JonTeaCz/CECS490-DR.PILL/Progress/Presentations/CECS 490A Progress Presentation 2.pdf

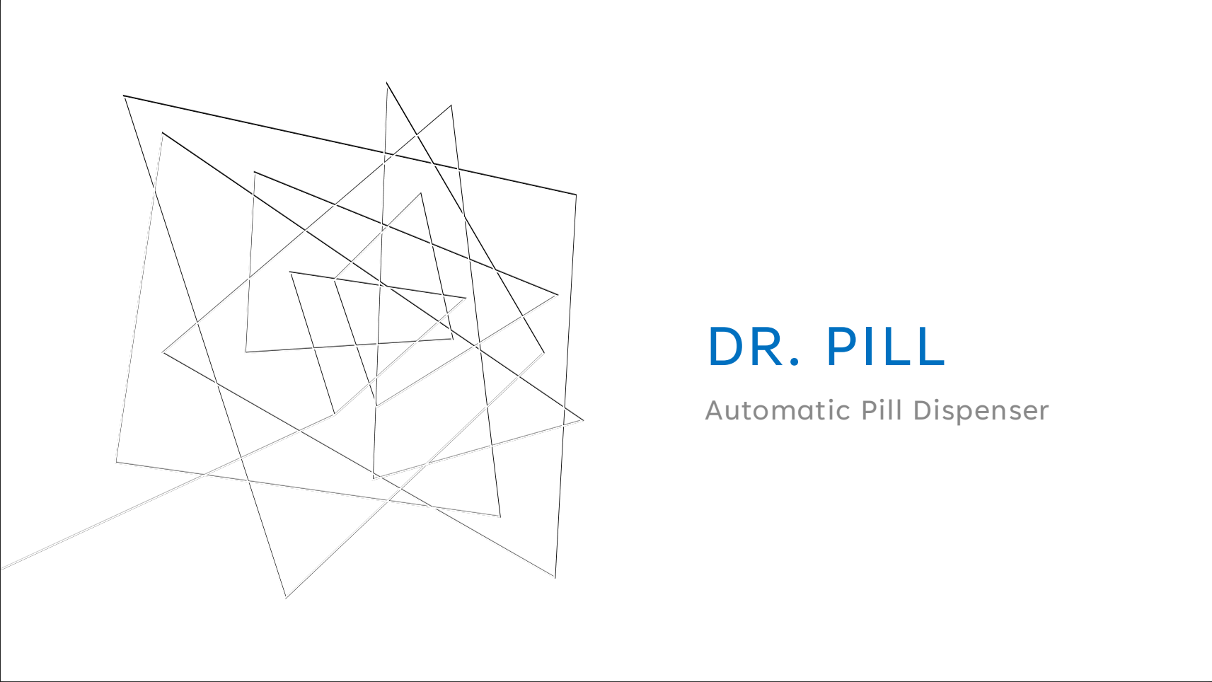
[picture p87: page 1]

# DR. PILL

# Automatic Pill Dispenser

# TEAM & ROLES

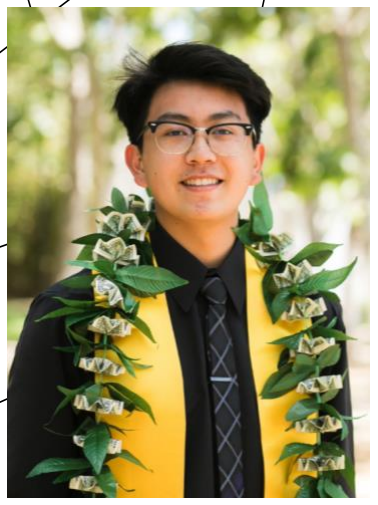
[picture p88: figure]

### - Power Supply & Regulation

## Jonathan Cerniaz

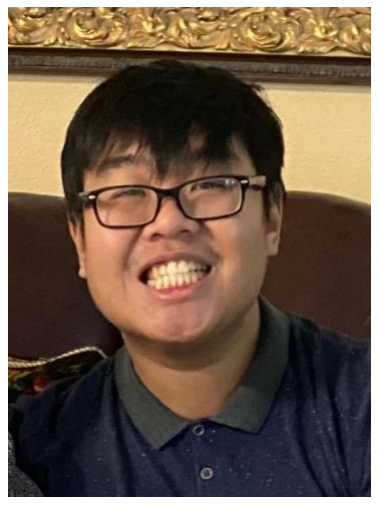
[picture p89: figure]

## Jehmel Espiritu

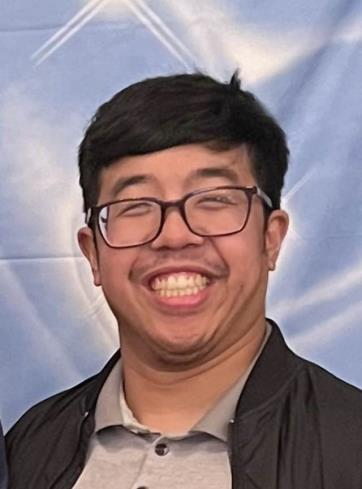
[picture p90: figure]

## Jeremy Espiritu

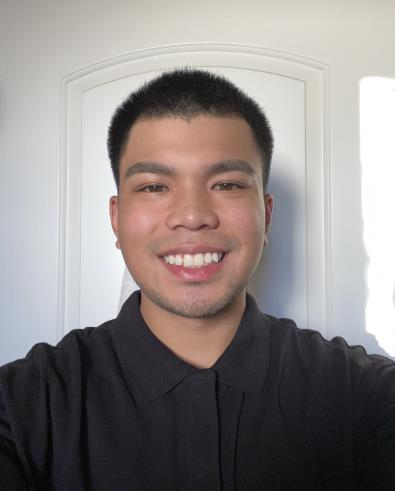
[picture p91: figure]

## Joseph Guzman

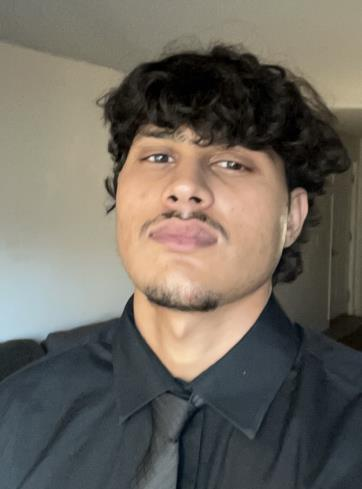
[picture p92: figure]

## Afzal Hakim

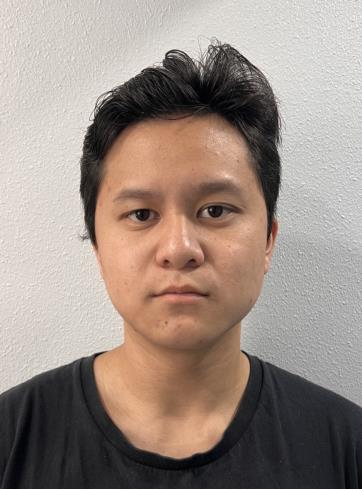
[picture p93: figure]

## Lee Roger Ordinario

### - Software Development of Interface

### - Log tracking and Security

### - Pill Storage System and Organization

### - Software Development of Interface

### - 3D Designing and Motor Testing for dispense mechanism

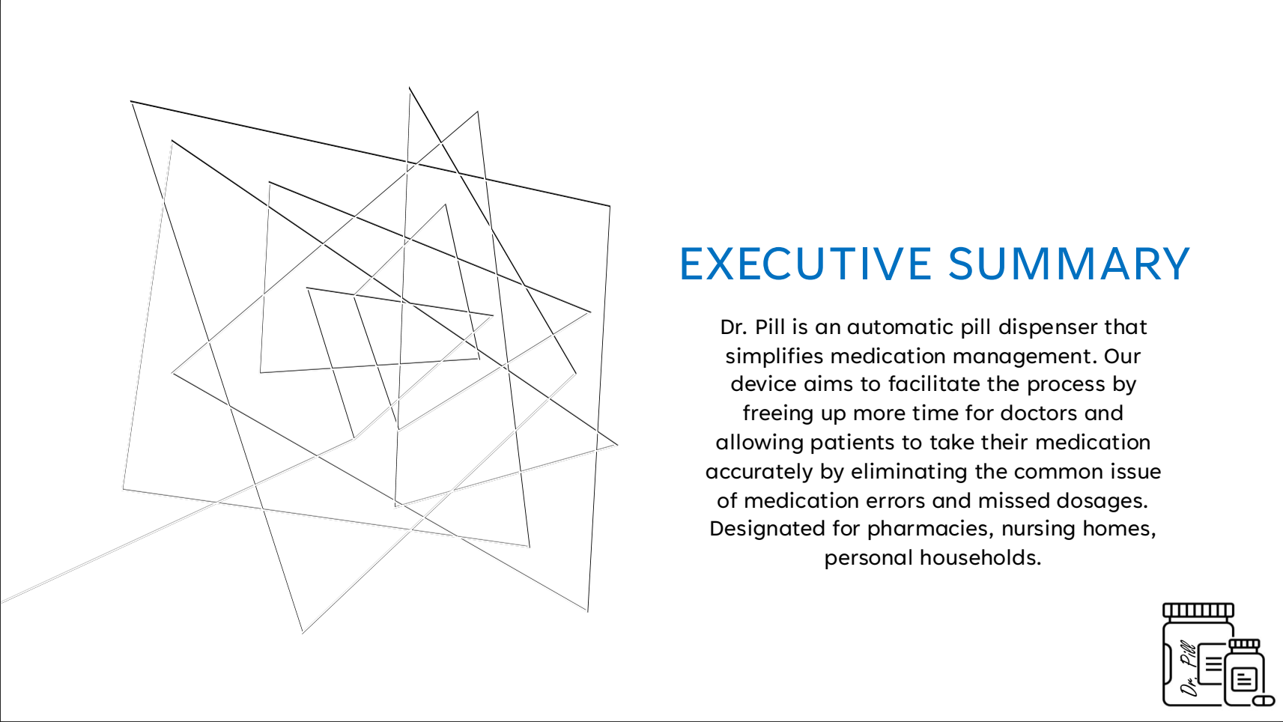
[picture p94: page 3]

# EXECUTIVE SUMMARY

## Dr. Pill is an automatic pill dispenser that simplifies medication management. Our device aims to facilitate the process by freeing up more time for doctors and allowing patients to take their medication accurately by eliminating the common issue

of medication errors and missed dosages. Designated for pharmacies, nursing homes, personal households.

## Dr. Pill

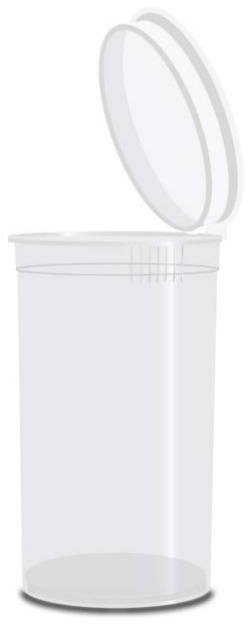
[picture p95: figure]
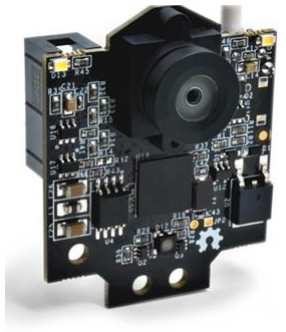
[picture p96: figure]

DISPENSE MECHANISM • Two Modes: Refill and On-demand o Refill: continuous dispensing of multiple pills

## of the same type

- On

## -demand: Needed number of dosage

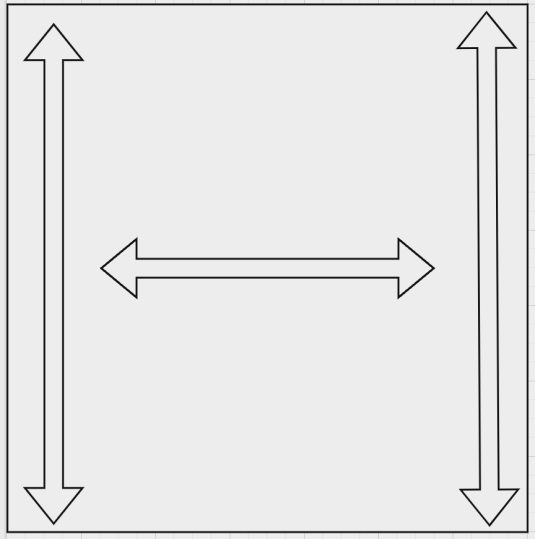
[picture p97: figure]

## dispensed at scheduled time

## - Object Recognition o To verify pill characteristics (color, size, pill

## shape, markings)

- Loading Mechanism for Grid o Use of Clear Prescription Bottles for visibility o Cross-contamination Prevention

## Dr. Pill Dr. Pill

## Features

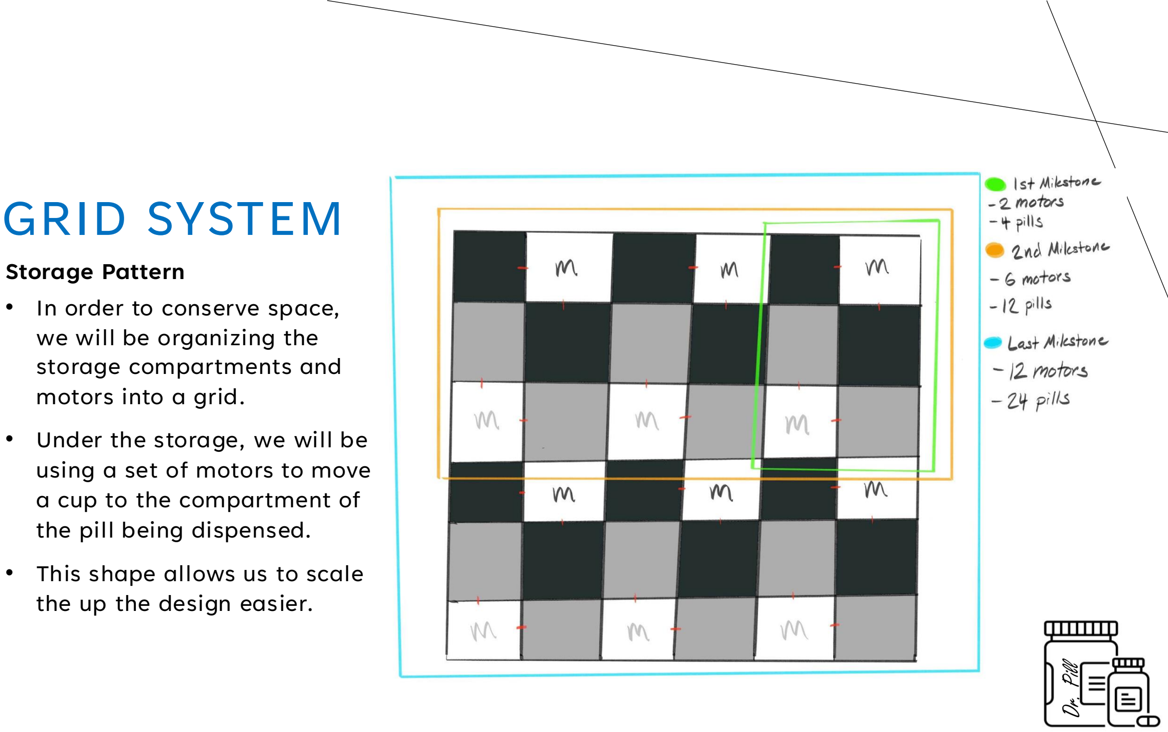
[picture p98: page 5]

# GRID SYSTEM

## Dr. Pill

## Storage Pattern

## Dr. Pill

- In order to conserve space,

## we will be organizing the storage compartments and

motors into a grid.

## - Under the storage, we will be using a set of motors to move a cup to the compartment of

the pill being dispensed.

## - This shape allows us to scale

the up the design easier.

# XAMPP

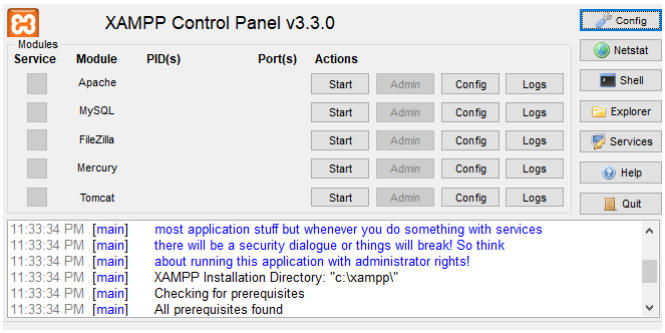
[picture p99: figure]

## Dr. Pill Dr. Pill

## - MySQL Database: We use this to store and manage logs such as user login

activity and pill requests.

## - Apache Server : This serves as the web server to handle user requests and

process PHP scripts.

# MYSQL DATABASE

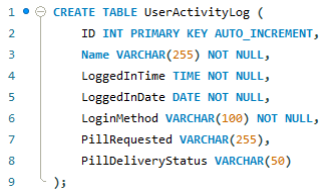
[picture p100: figure]

## Example code showing how the table columns for storing the data will be

structured.

## Dr. Pill Dr. Pill

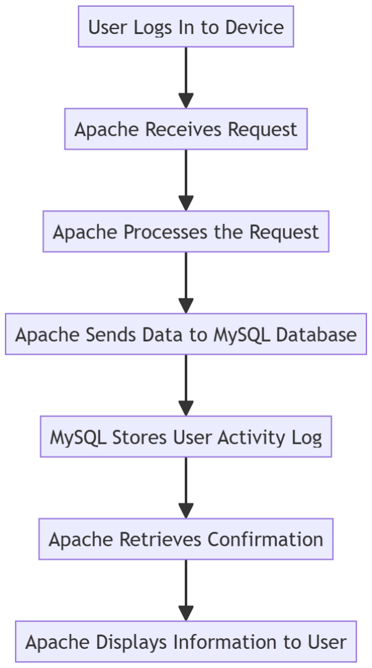
[picture p101: figure]

# APACHE

## Dr. Pill Dr. Pill

## - When a request is made for a PHP file, Apache processes the PHP code through the PHP interpreter in XAMPP and sends

the output back to the device.

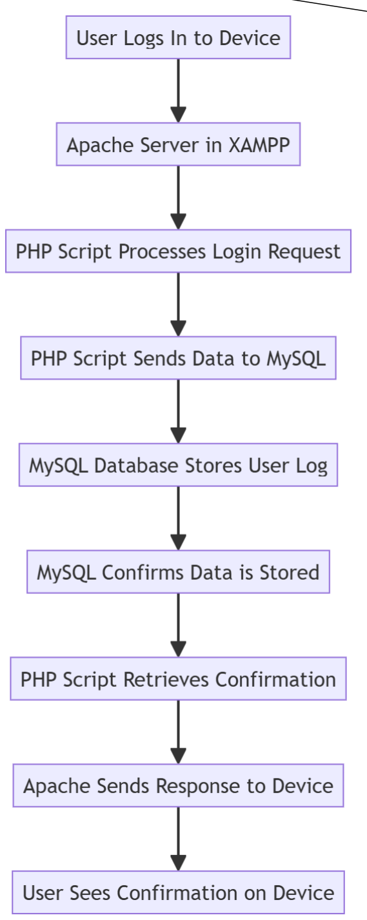
[picture p102: figure]

9

# SIMPLE FLOWCHART OF LOG TRACKING

# INTERFACE

## Features

## - User Authentication: uses MySQL database for secure login and credential storage

## - MySQL Database Integration: Central for storing user data, patient records, staff actions and logs

## - Permission checks: ensure secure, authorized actions

## - Guidance Prompts: if patient is denied, directs them to seek assistance with logs recorded

## Dr. Pill Dr. Pill

## Staff/Patient Input

## - Staff Input

## - Storage Management: Check and update inventory

## - Patient Management: Add/remove patient records

## - Logs Management: View history data

- Medication Retrieval: staff can retrieve medication,

## with actions logged onto the database

## - Patient Input

- Medication Retrieval: Permission-based access,

## logged onto the database

## - View History log: Patients access personal logs

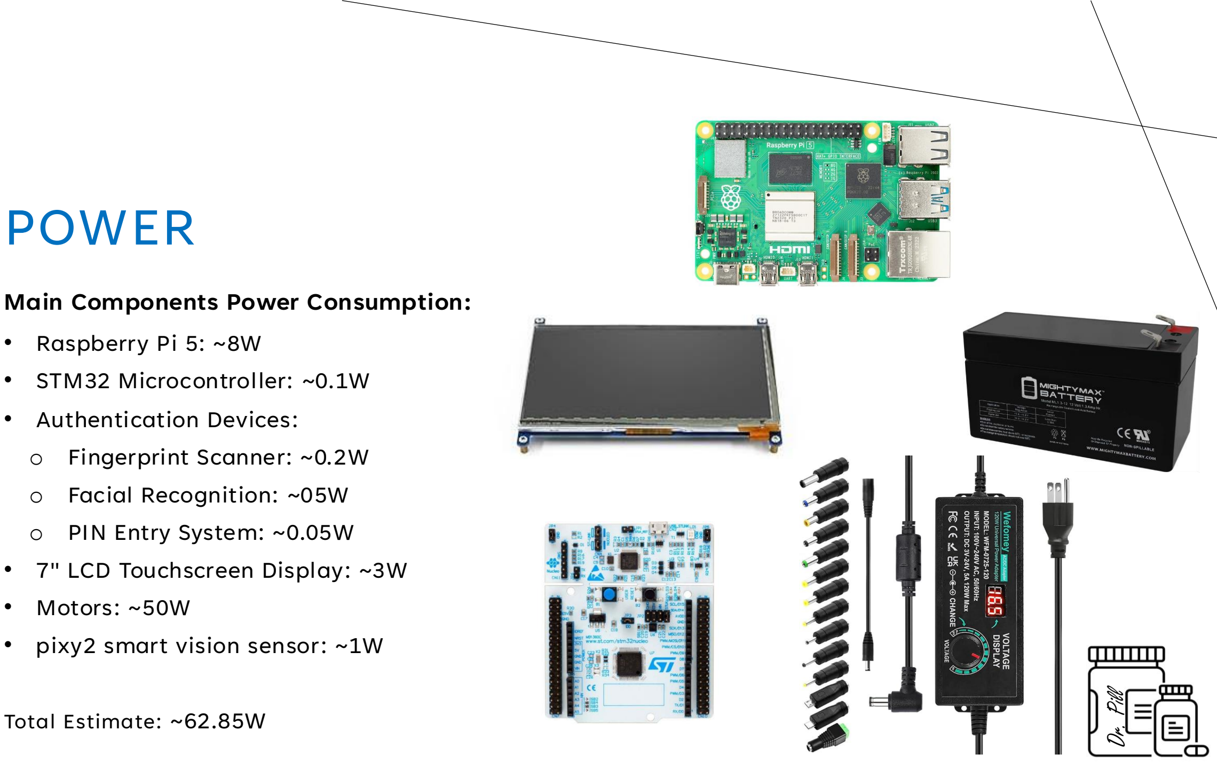
[picture p103: page 11]

# POWER

Main Components Power Consumption: • Raspberry Pi 5: ~8W • STM32 Microcontroller: ~0.1W • Authentication Devices: o | Fingerprint Scanner: ~0.2W o | Facial Recognition: ~05W o | PIN Entry System: ~0.05W • 7" LCD Touchscreen Display: ~3W • Motors: ~50W • pixy2 smart vision sensor: ~1W

## Total Estimate: ~62.85W

## Dr. Pill Dr. Pill

## Dr. Pill

# PROGRESS

What was planned but not accomplished? | What was planned and accomplished?

## - Grid System for retrieving pills from storage - MySQL Database for tracking logs - Apache Server to handle user request and process PHP scripts - Physical 3D print of our dispense mechanism

## - Object recognition for identification of pills as well as the placement for the device

## - Circuit management and power consumption

## - Software development for our dispensing mechanism

## - Develop a user interface for patients and authorized personnel

# TIMELINE

### Aug

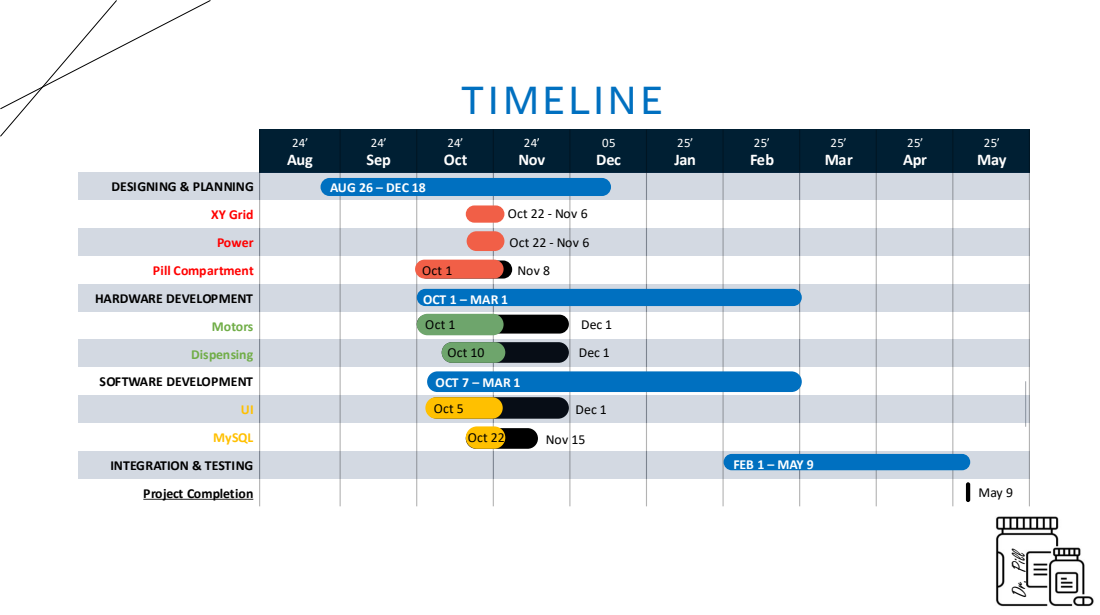
[picture p104: page 13]
Dr. Pill; 24’ Sep; 24’ Oct; 24’ Nov; 05 Dec; 25’ Jan; 25’ Feb; 25’ Mar; 25’ Apr; 25’ May; DESIGNING & PLANNING; XY Grid; Power; Pill Compartment; HARDWARE DEVELOPMENT; Motors; Dispensing; SOFTWARE DEVELOPMENT; MySQL; INTEGRATION & TESTING; Project Completion; Oct 22 - Nov 6; Nov 8; Oct 1; Oct 5; Oct 22; FEB 1 – MAY 9; May 9; OCT 7 – MAR 1; OCT 1 – MAR 1; AUG 26 – DEC 18; Oct 10; Nov 15; Dec 1

Alam, Md Tausif, et al. “FDA-Approved Natural Polymers for Fast Dissolving Tablets.” Journal of Pharmaceutics, U.S. National Library of Medicine, https://www.ncbi.nlm.nih.gov/pmc/articles/PMC4590815/

Alei. “Pill Size Chart.” AIPAK, 9 Apr. 2024, www.icapsulepack.com/pill-size-chart/.

Budibase. “How to Build a SQL GUI in Minutes | Budibase.” Budibase Blog, https://budibase.com/blog/tutorials/sql-gui/

Charlesworth, Christina J, et al. “Polypharmacy Among Adults Aged 65 Years and Older in the United States: 1988-2010.” The Journals of Gerontology. Series A, Biological Sciences and Medical Sciences, U.S. National Library of Medicine, www.ncbi.nlm.nih.gov/pmc/articles/PMC4573668/.

Craig M. Hales, M.D., M.P.H., Jennifer Servais, B.Sc., Crescent B. Martin, M.P.H., M.A., and Dafna Kohen, Ph.D., M.Sc., “Products - Data Briefs -Number 347 - August 2019.” Centers for Disease Control and Prevention, 14 Aug. 2019, https://www.cdc.gov/nchs/products/databriefs/db347.htm#:~:text=Among%20U.S.%20adults%20aged%2060,proton%20pump%20inhibitors%20(16.9%25/ (https://www.cdc.gov/nchs/products/databriefs/db347.htm)

Embedded._.programmer. "Raspberry pi setup with 7 inch touch screen." YouTube, 22 Oct. 2022, www.youtube.com/watch?v=hVn4-GMF7Eg.

Ferro Uriguen, Alexander, et al. “Determination of the Cross-Contamination and Validation of the Cleaning Process for an Automated Personalised Dosing System.” European Journal of Hospital Pharmacy : Science and Practice, U.S. National Library of Medicine, www.ncbi.nlm.nih.gov/pmc/articles/PMC9047934/.

Formlabs, “The Essential Guide to Food Safe 3D Printing.” Formlabs, formlabs.com/blog/guide-to-food-safe-3d-printing/.

Gaikwad, Manjiri. "Running SQL Server on Raspberry Pi Using Docker | A 101 Guide." Hevo Data, 31 July 2022, https://hevodata.com/learn/sql-
server-on-raspberry-pi/. (https://hevodata.com/learn/sql-server-on-raspberry-pi/)

## Dr. Pill

# REFERENCES

## Dr. Pill

"How to Control Servo Motors with a Raspberry Pi." Digi-Key Electronics, www.digikey.com/en/maker/tutorials/2021/how-to-control-servo-motorswith-a-raspberry-pi. (http://www.digikey.com/en/maker/tutorials/2021/how-to-control-servo-motors-with-a-raspberry-pi)

"How to Setup Raspberry Pi for Beginners." YouTube, uploaded by Bytesized_Raspberry_Pi, 23 Dec. 2021, youtu.be/N_lbMR6_EBA.

J. Mark Ruscin, Sunny A. Linnebur, “Aging and Medications - Aging and Medications.” Merck Manual Consumer Version, www.merckmanuals.com/home/older-people%E2%80%99s-health-issues/aging-and-medications/aging-and-medications.

"Pharmaceutical Packaging Design Tips for Improved Safety." Luminite, blog.luminite.com/blog/pharmaceutical-packaging-design-tips-forimproved-safety. (http://blog.luminite.com/blog/pharmaceutical-packaging-design-tips-for-improved-safety)

“Pill Counting Scales.” DSCBalances, www.dscbalances.com/collections/pill-counting-scales.

Ranjit’s Embedded Solutions, “Arduino-based Conveyor Belt Using DC Motor with RPM Control And Object Counting”, YouTube, www.youtube.com/watch?v=VHAqJ9a7SqI.

Rosemont Pharma, “Rosemont: Information For Patients On The Dangers Of Tablet Crushing.”, 14 Oct. 2023, www.rosemontpharma.com/tabletcrushing/. (http://www.rosemontpharma.com/tablet-crushing/)

Running SQL Server on Raspberry Pi Using Docker | A 101 Guide." YouTube, uploaded by Hevo Data, 31 July 2022, https://youtu.be/uS9VvnJWoxs.
UI Bakery. “How to Build a Custom SQL Database GUI | UI Bakery.” YouTube, 20 Oct. 2020, https://www.youtube.com/watch?v=FGDwVagO1XI.

# REFERENCES

## Dr. Pill

# REFERENCES

## Dr. Pill

Wang, Nathan, “What Is PLA Plastic? Benefits, Uses, and Safety of PLA Material!” Onenice Internaional Co., Ltd., 30 July 2024, www.geckohaha.com/what-is-pla-plastic/.

YouTube: Best Automatic Pill Dispensers [November 2021], www.youtube.com/watch?v=ffu1d6DnqjQ.

YouTube: Count Right Pill Counter (J1245n) - Inventory, www.youtube.com/watch?v=l1ECQJ63jCg.

YouTube: Electronic Tablet Counter: RX 4 Capsule Counter Machine by RX Count, www.youtube.com/watch?v=mO_NhPjw8f0.

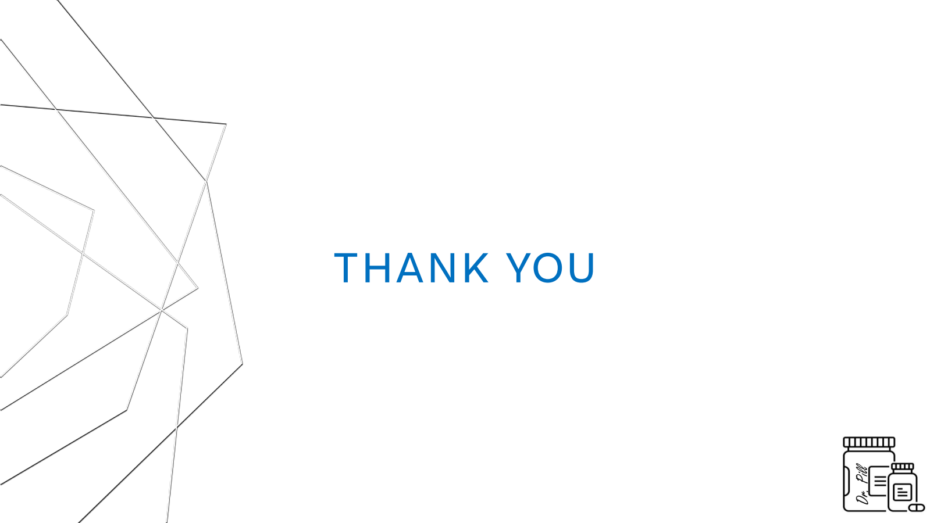
[picture p105: page 17]

# THANK YOU

## Dr. Pill
