JonTeaCz/CECS490-DR.PILL/Progress/Presentations/CECS 490B - Demonstration 1 Presentation.pdf

# DR. PILL

Automatic Pill Dispenser

## MEET THE TEAM


- Power Supply
& Regulation
- Circuit Design

Jonathan
Cerniaz


Jehmel
Espiritu


Jeremy
Espiritu


Joseph
Guzman


Afzal
Hakim


Lee Roger
Ordinario
- Software
Development
of Interface
- Log tracking
and Security
- Pill Storage
System and
Organization
- Soldering
- Software
Development
of Interface
- System prototyping
and calibration
- 3D Design

## PROJECT OVERVIEW

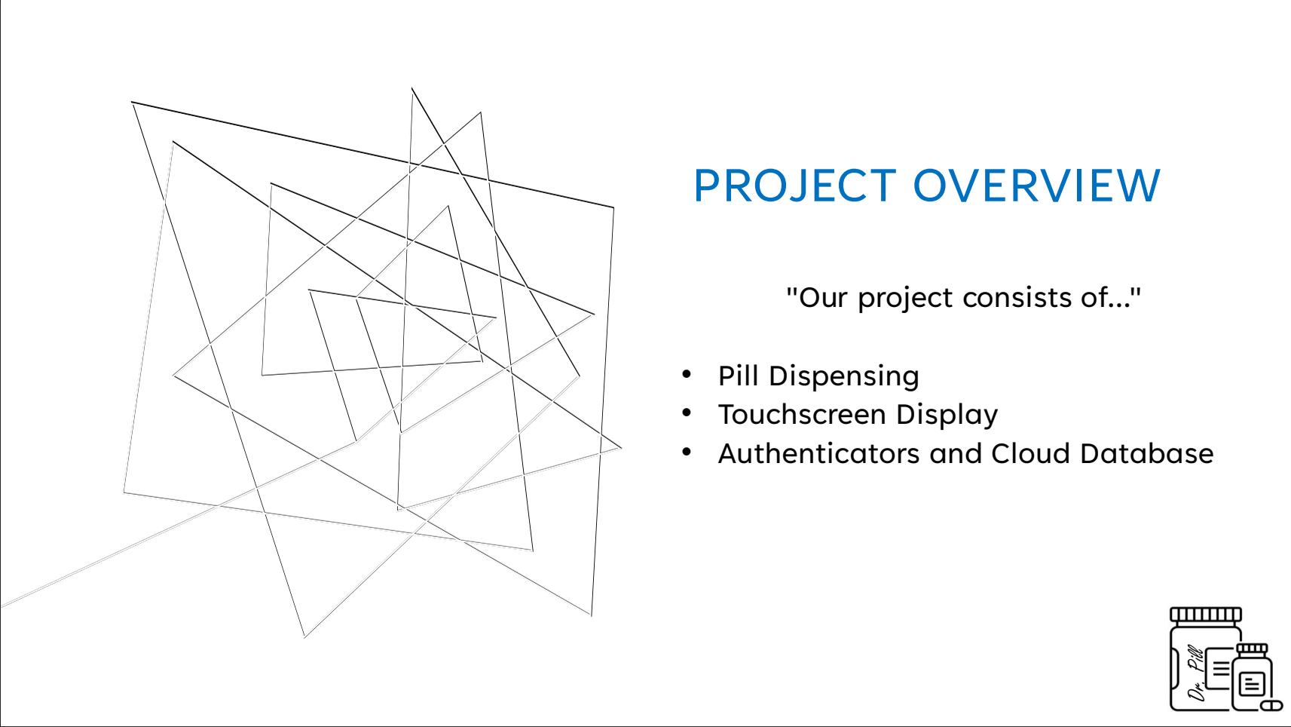
[picture p106: page 3]

Dr. Pill

"Our project consists of..."

- Pill Dispensing
- Touchscreen Display
- Authenticators and Cloud Database

## OUR 3 DEMOS

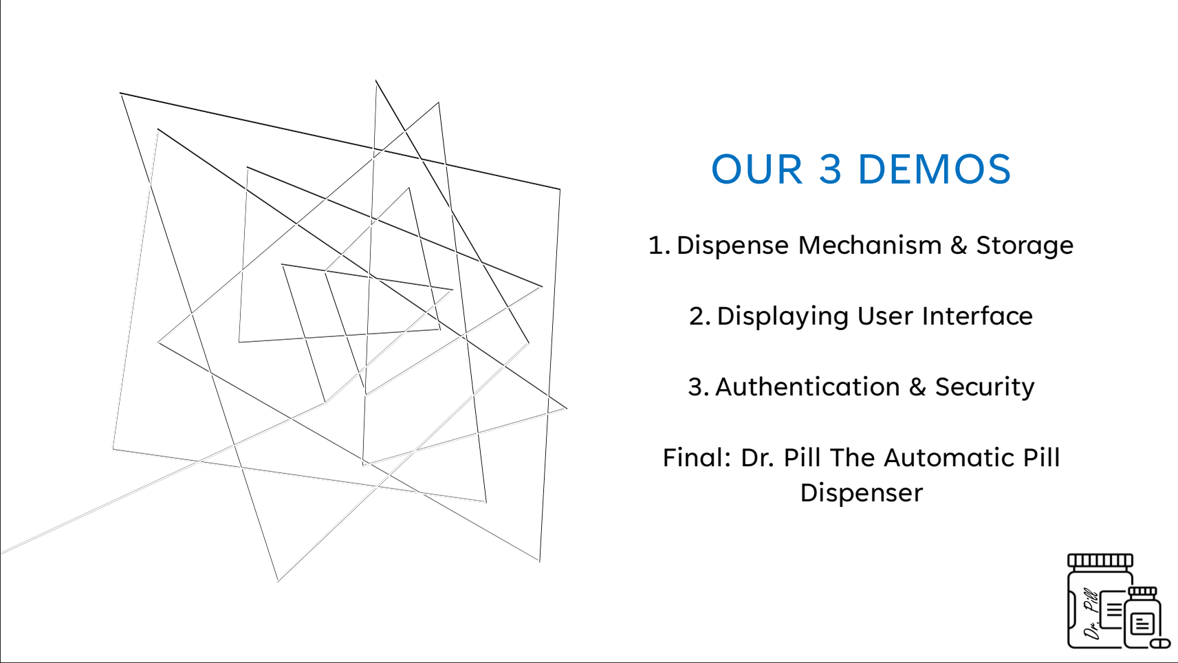
[picture p107: page 4]

Dr. Pill

1.Dispense Mechanism & Storage

2.Displaying User Interface

3.Authentication & Security

Final: Dr. Pill The Automatic Pill Dispenser

5

## TODAY'S DEMO

Dispense Mechanism and Storage

Requirements: Drop system, storage compartments with funnel, 2 different pills minimum, correct amount of pills dropped

Constraints: Power Consumption, Motor Accuracy, Pill Dispensing Accuracy

Success: Correct pills and amount dispensed, motor efficiently moves, storage dispenses pills smoothly

Dr. Pill

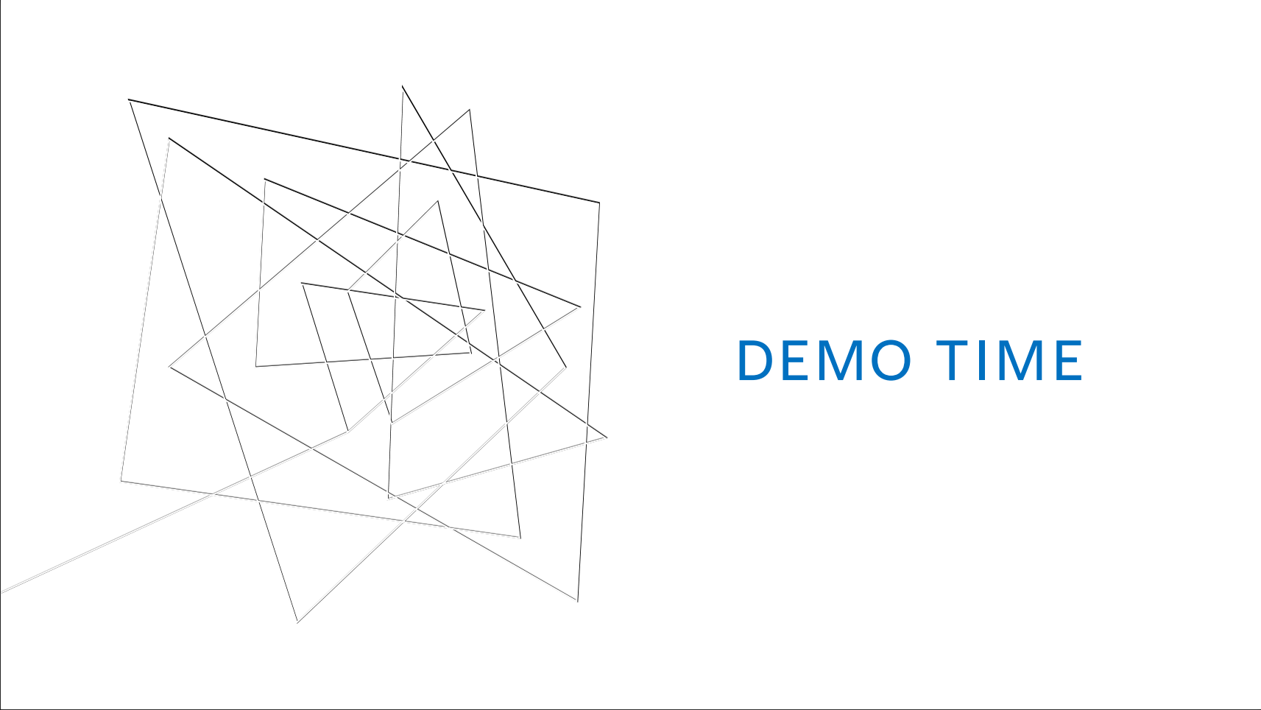
[picture p108: page 6]

# DEMO TIME

## TECHNICAL DETAILS

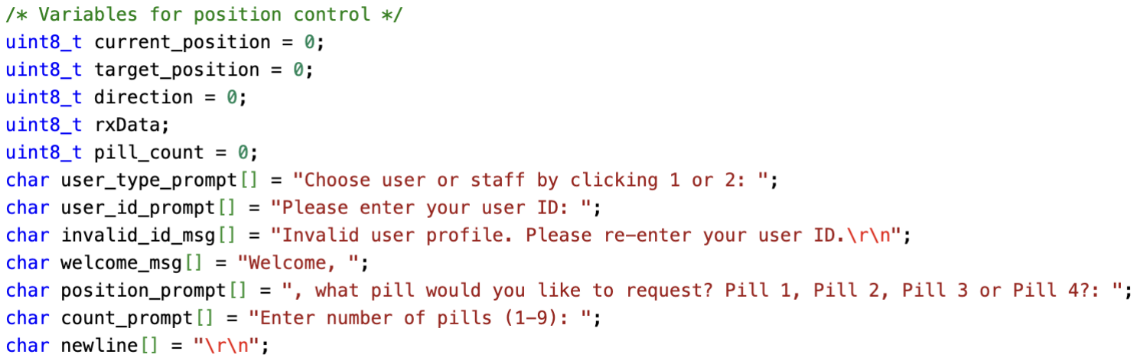
[picture p109: figure]

7 Dr. Pill

## TECHNICAL DETAILS

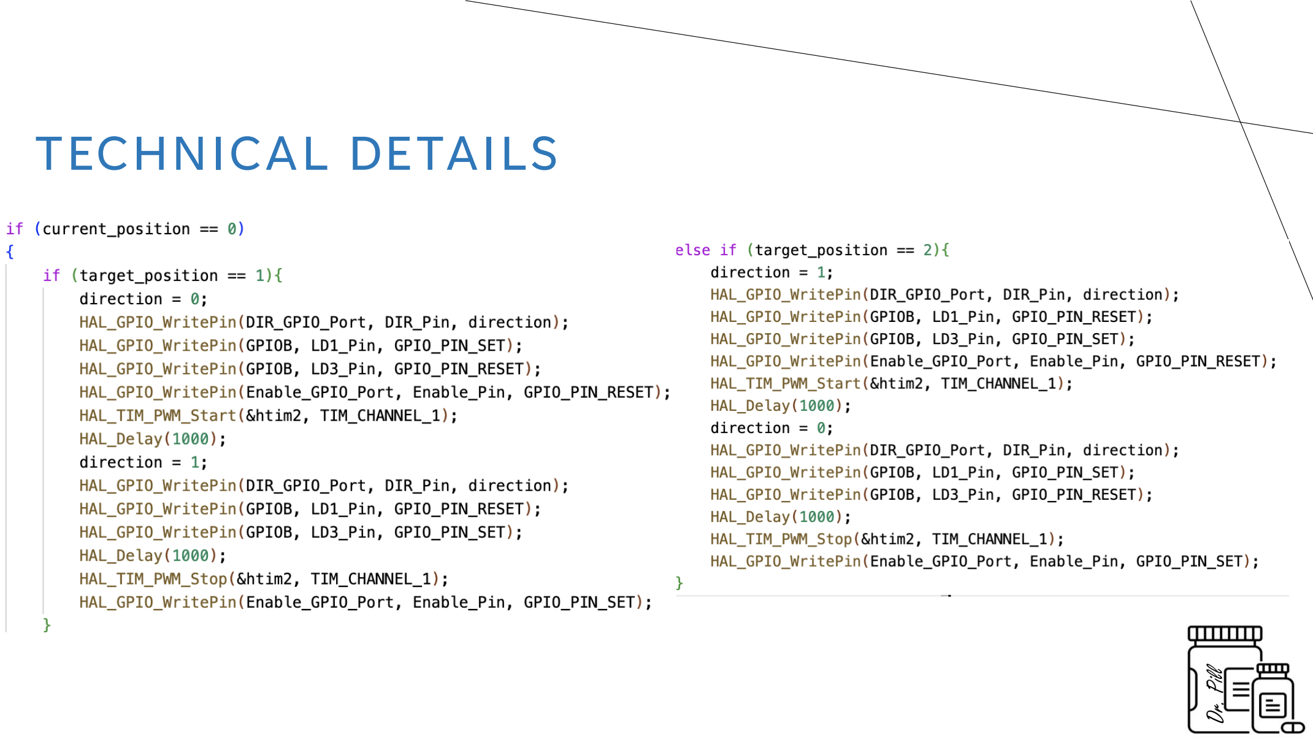
[picture p110: page 8]

8

Code snippets

Dr. Pill

## TECHNICAL DETAILS

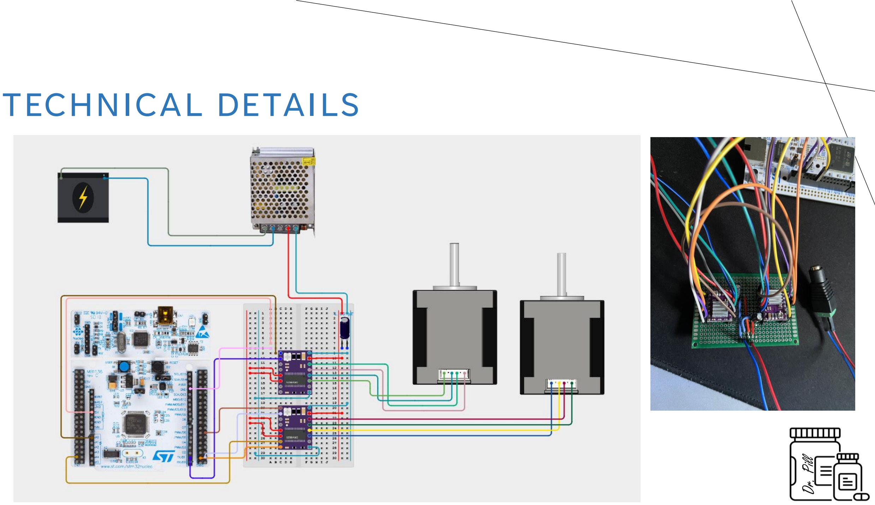
[picture p111: page 9]

9 Dr. Pill

## TECHNICAL DETAILS

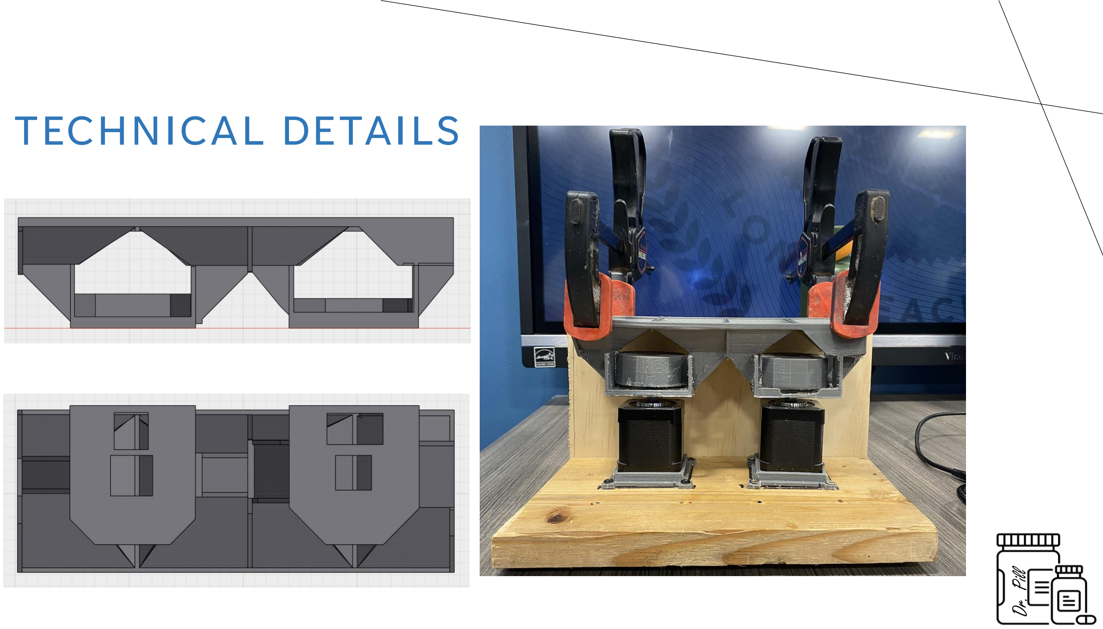
[picture p112: page 10]

10 Dr. Pill

## TECHNICAL DETAILS

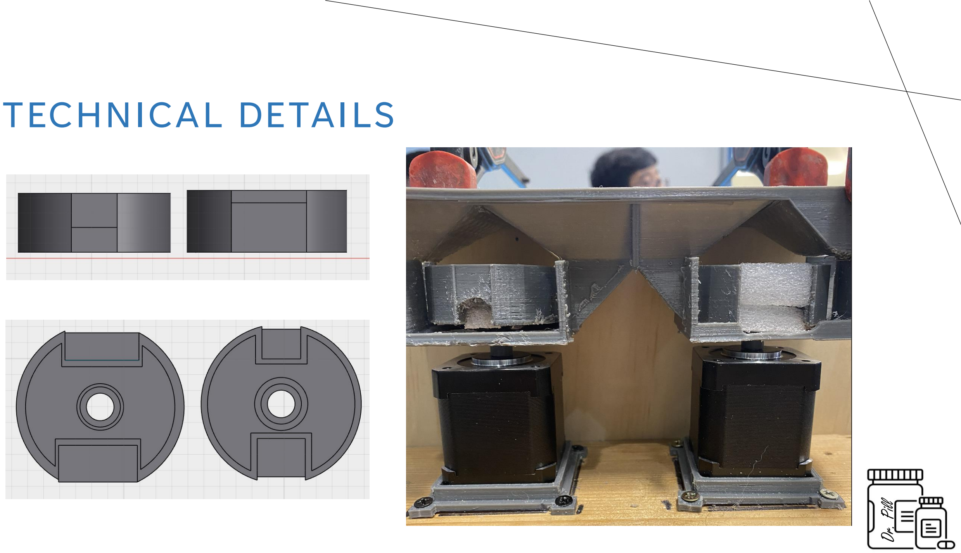
[picture p113: page 11]

11 Dr. Pill

## CHALLENGES

12

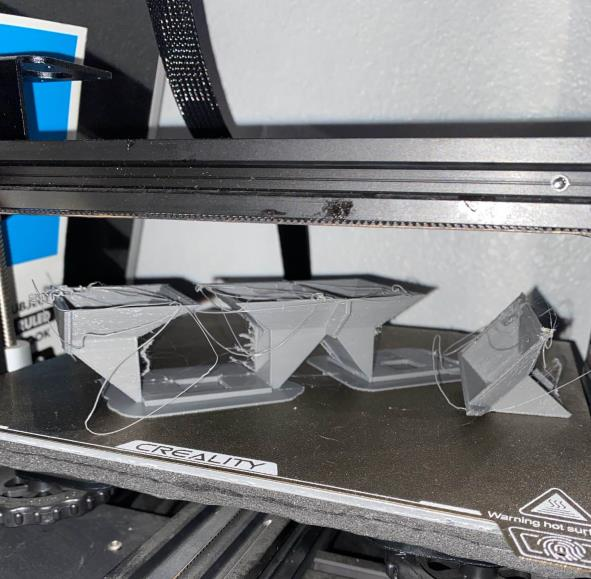
[picture p114: figure]
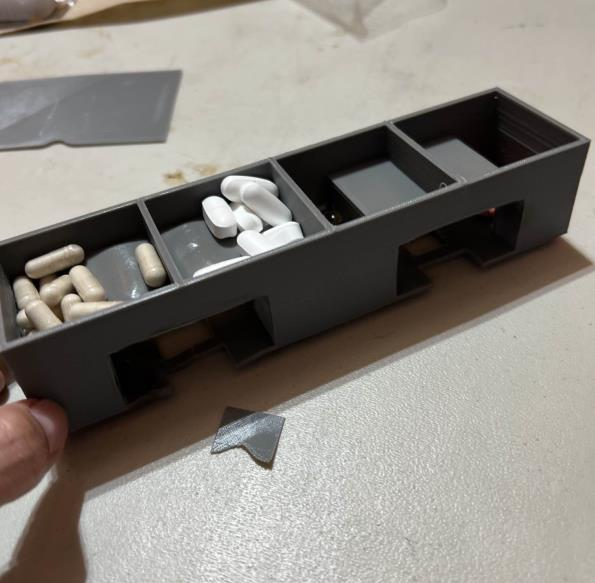
[picture p115: figure]
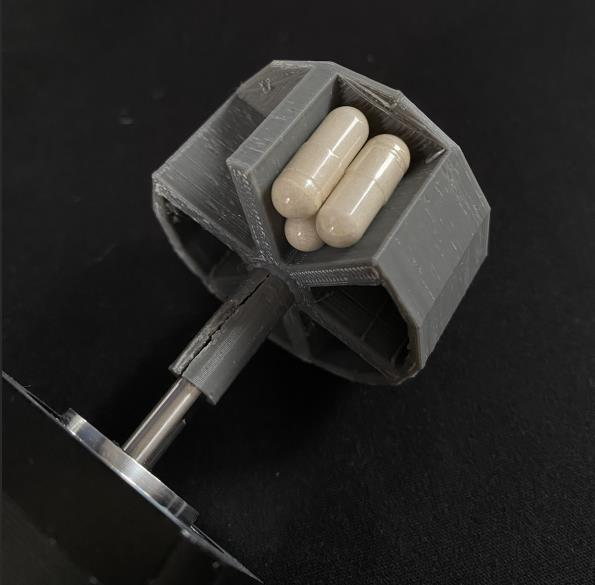
[picture p116: figure]

Printing time | Pocket refill | Printing Dimensions

Dr. Pill

## OVERCOMING CHALLENGES

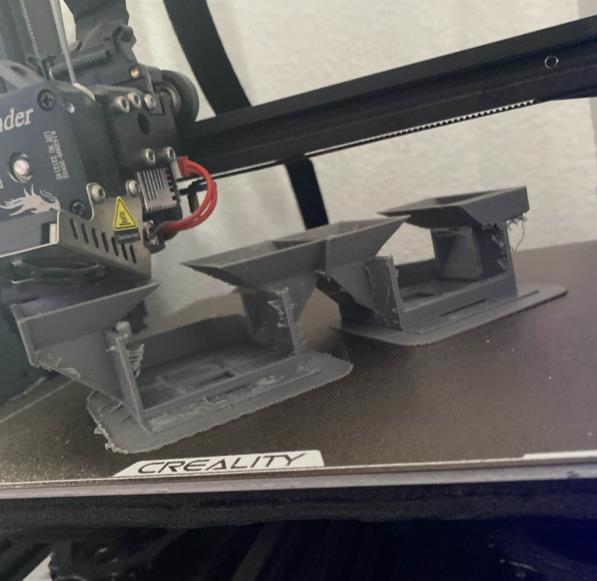
[picture p117: figure]
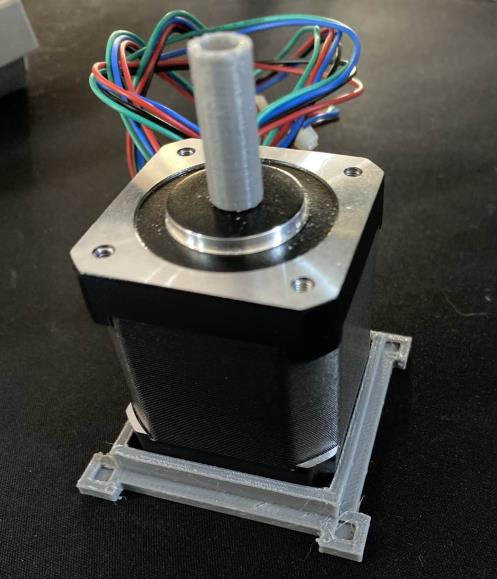
[picture p118: figure]

13

Printing Time
- Redesign pocket and storage to lower material and time required without compromising the stability of the design. Simplifying the design, making it easier to recreate/expand on for later demos.

Pocket refill
- So we don’t have to reprint too many times, we decided to have the funnel and pocket be open to customize based on the pill we will test. Pockets will be replaceable depending on the pill.

Dr. Pill

14

## NEXT DEMO

DISPLAYING USER INTERFACE

Requirements: Touchscreen LCD Display, Raspberry Pi 5

Success: Responds accurately and consistently, Terminal displays correctly on the LCD

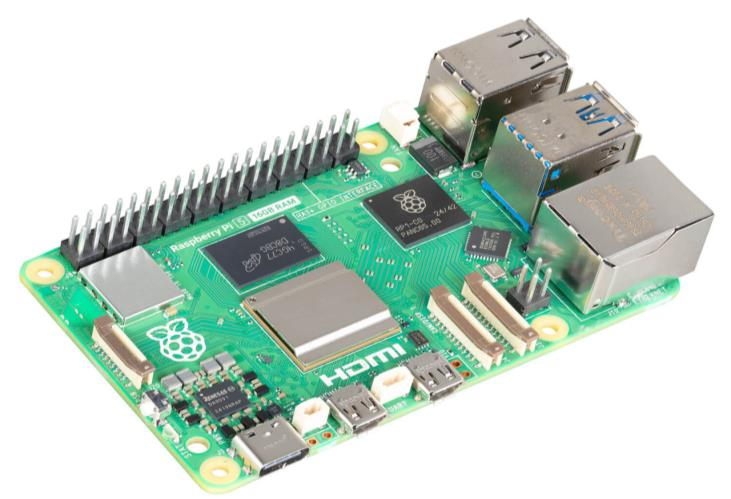
[picture p119: figure]
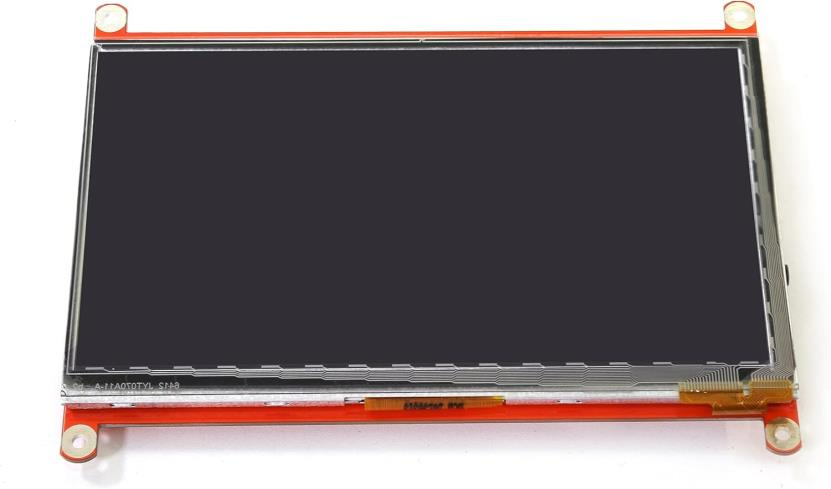
[picture p120: figure]

Dr. Pill


# THANK YOU

Dr. Pill
