JonTeaCz/CECS490-DR.PILL/Progress/Presentations/CECS 490B - Demonstration 3 Presentation.pdf

# DR. PILL

Automatic Pill Dispenser

## MEET THE TEAM


- Fingerprint and
Facial Recognition
- Circuit Design

Jonathan
Cerniaz


Jehmel
Espiritu


Jeremy
Espiritu


Joseph
Guzman

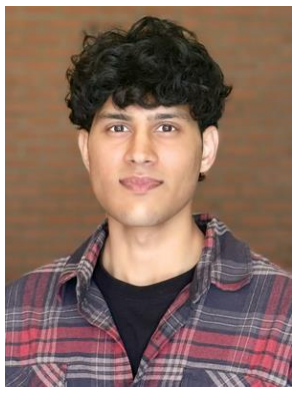
[picture p121: figure]

Afzal
Hakim


Lee Roger
Ordinario
- Software
Development
of Interface
- Fingerprint and
Facial Recognition
- Log tracking and
Security
- Pill Storage
System and
Organization
- PCB Design
and Soldering
- Software
Development
of Interface
- Object Recognition
- Board to Board
Communication
- 3D Design

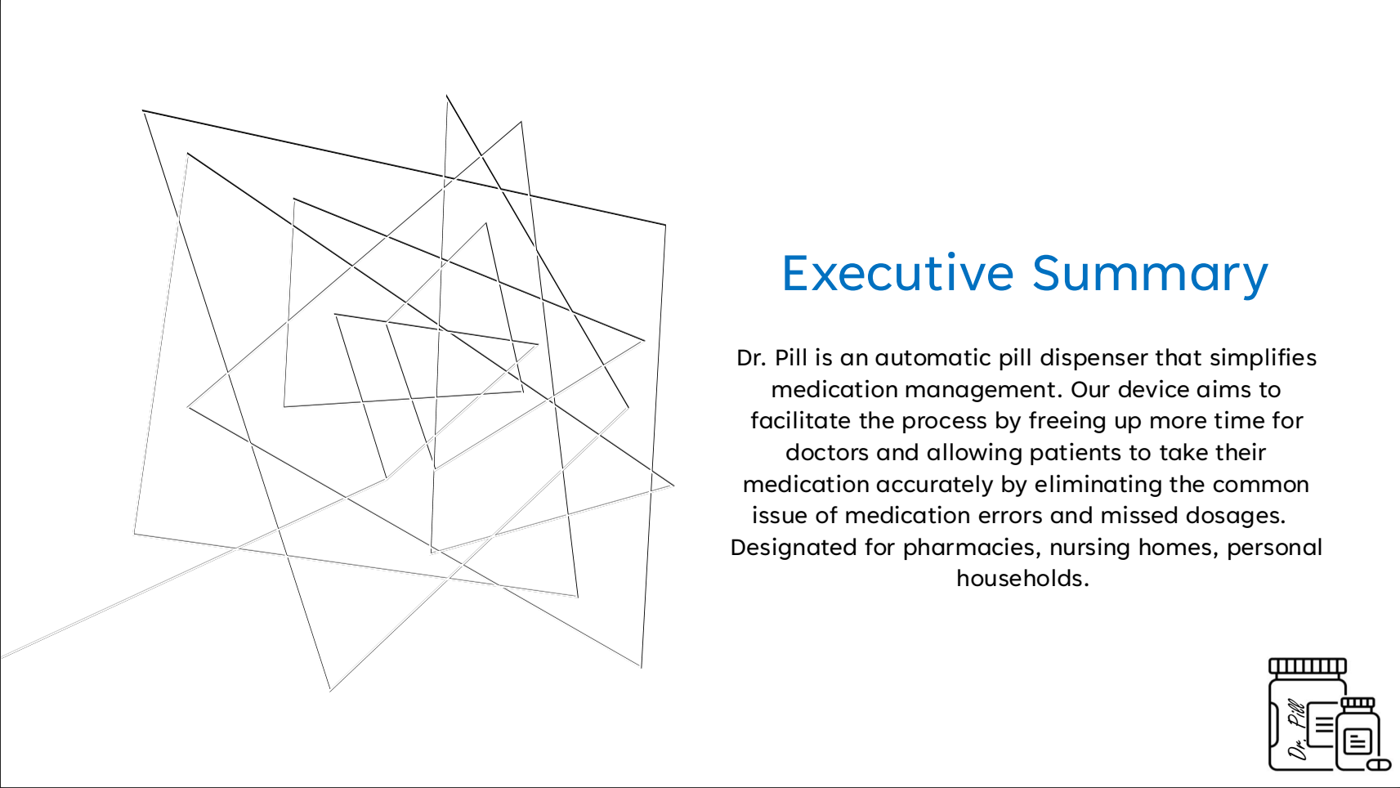
[picture p122: page 3]

## Executive Summary

Dr. Pill

Dr. Pill is an automatic pill dispenser that simplifies medication management. Our device aims to facilitate the process by freeing up more time for doctors and allowing patients to take their medication accurately by eliminating the common issue of medication errors and missed dosages. Designated for pharmacies, nursing homes, personal households.

## OUR 3 DEMOS

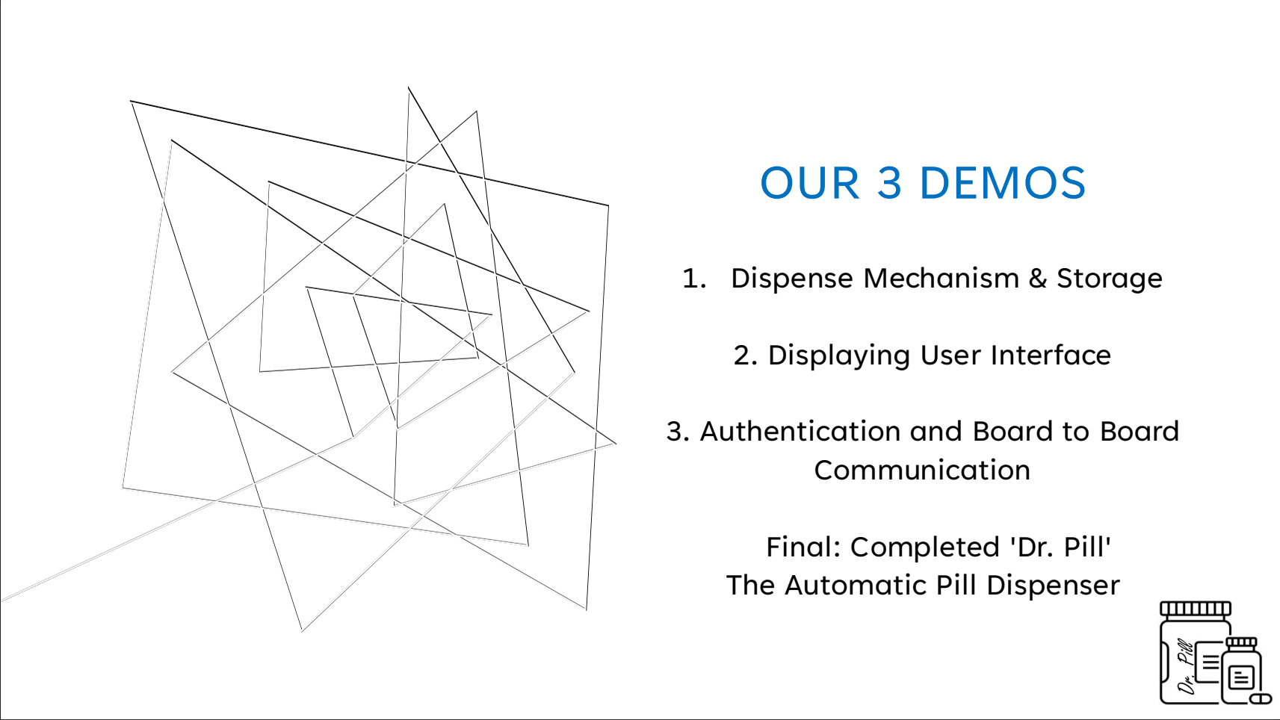
[picture p123: page 4]

Dr. Pill

1. Dispense Mechanism & Storage
2. Displaying User Interface
3. Authentication and Board to Board Communication

Final: Completed 'Dr. Pill' The Automatic Pill Dispenser

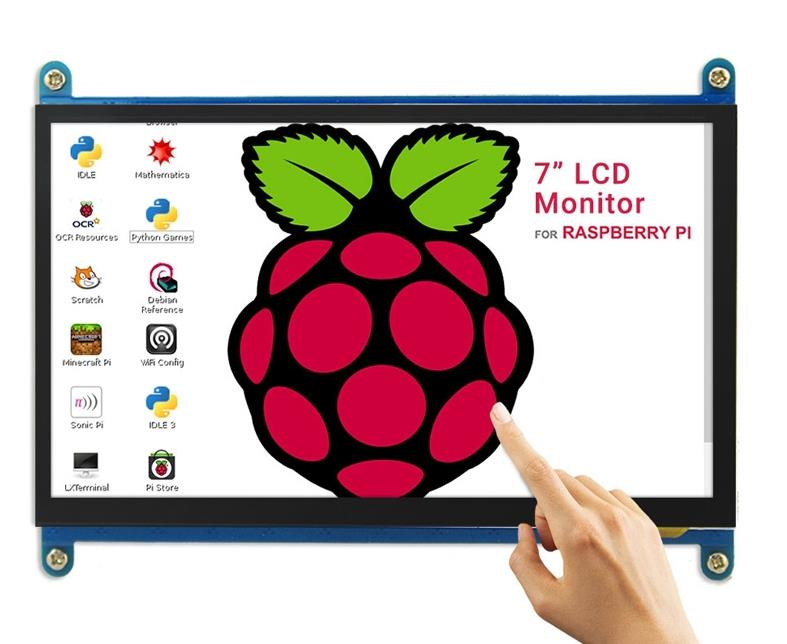
[picture p124: figure]
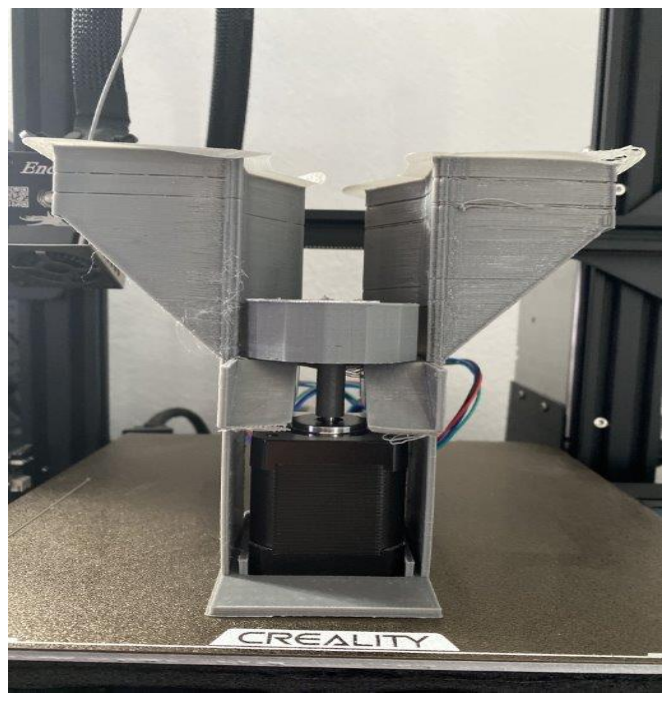
[picture p125: figure]

5

## PREVIOUS DEMONSTRATION

Dr. Pill

1. 3D Design (Dispense Mechanism & Storage) (Computer <--> MobaXTerm <--> STM32/Motors)
2. Displaying User Interface (RaspberryPi/LCD <--> MobaXTerm <--> STM32/Motors)

6

## TODAY'S DEMO

Authentication and Board to Board Communication

Requirements: Fingerprint and Facial Recognition working for specified users, object detecting different pills

Constraints: Authentication devices accuracy and Motor response from GUI input

Success: Fingerprint and facial recognition sensor successfully integrated with our GUI.

Dr. Pill


# DEMO TIME

## TECHNICAL DETAILS

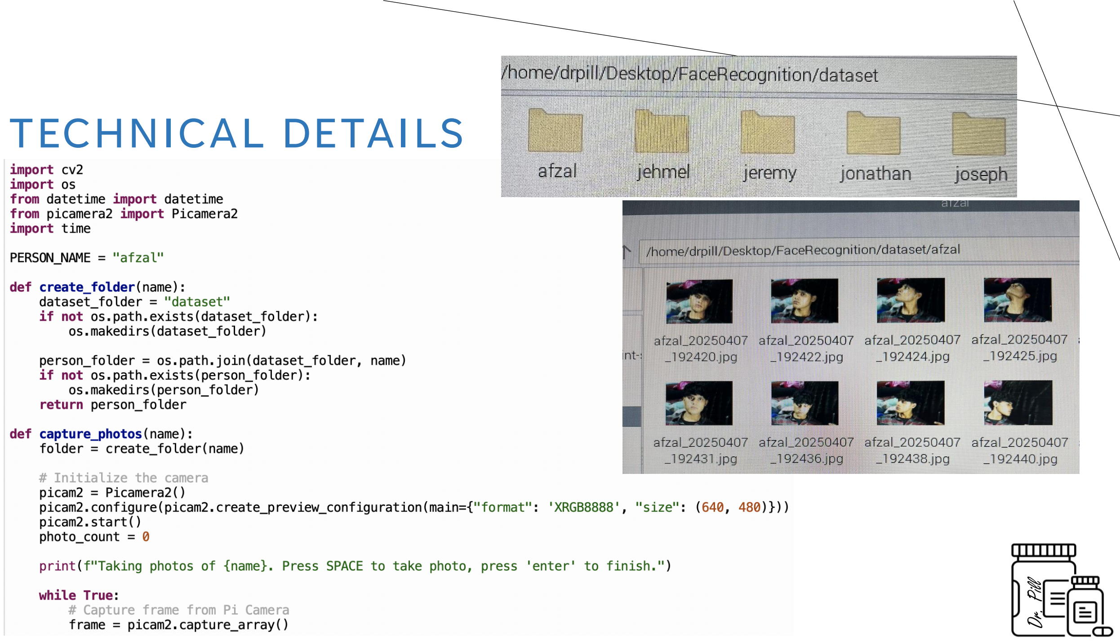
[picture p126: page 8]

8 Dr. Pill

## TECHNICAL DETAILS

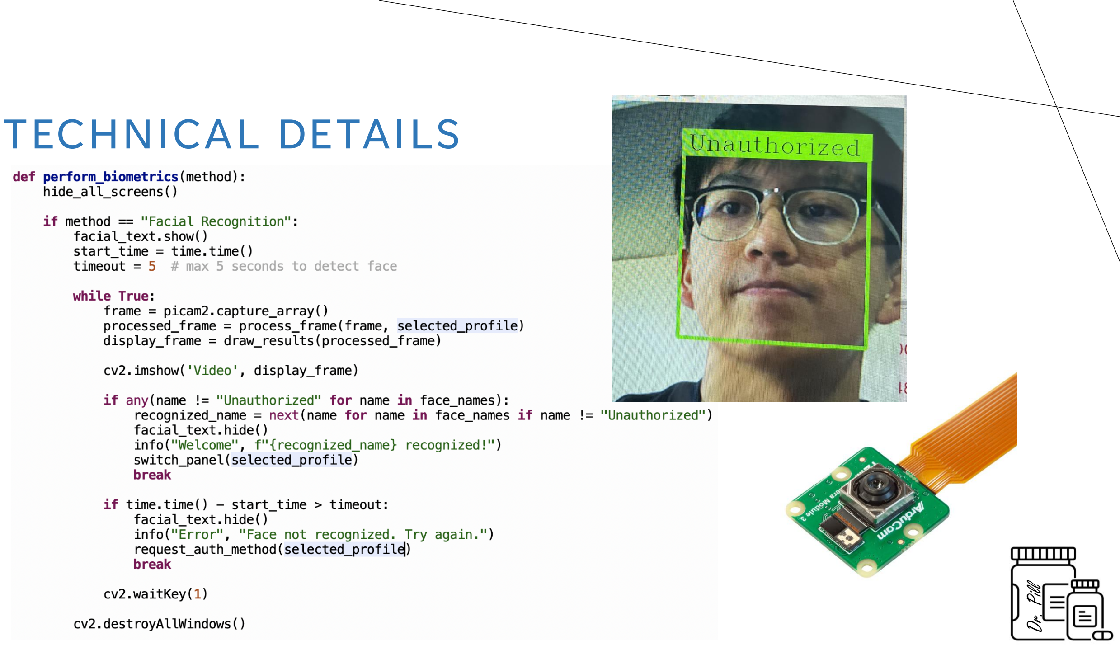
[picture p127: page 9]

9 Dr. Pill

## TECHNICAL DETAILS

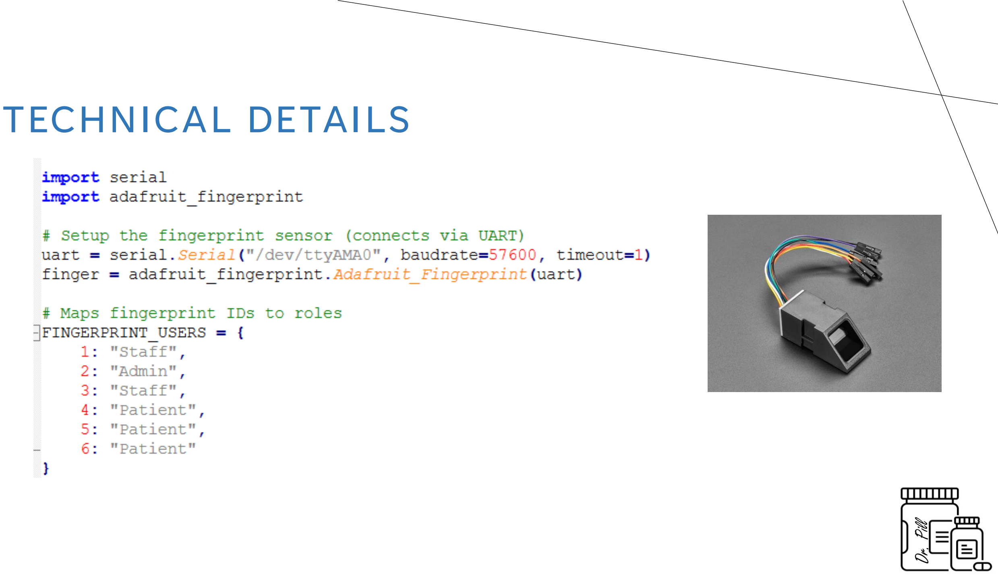
[picture p128: page 10]

10 Dr. Pill

## TECHNICAL DETAILS

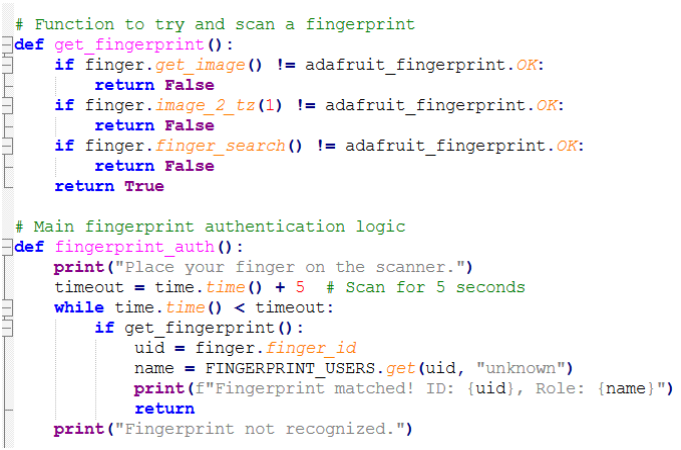
[picture p129: figure]

11 Dr. Pill

## TECHNICAL DETAILS

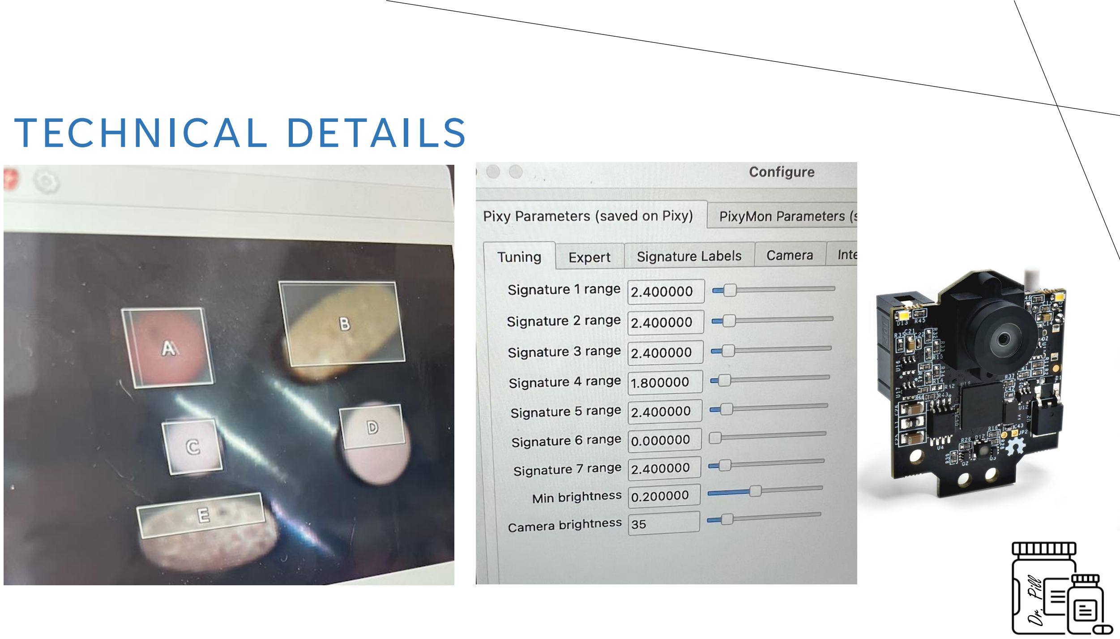
[picture p130: page 12]

12 Dr. Pill

## TECHNICAL DETAILS

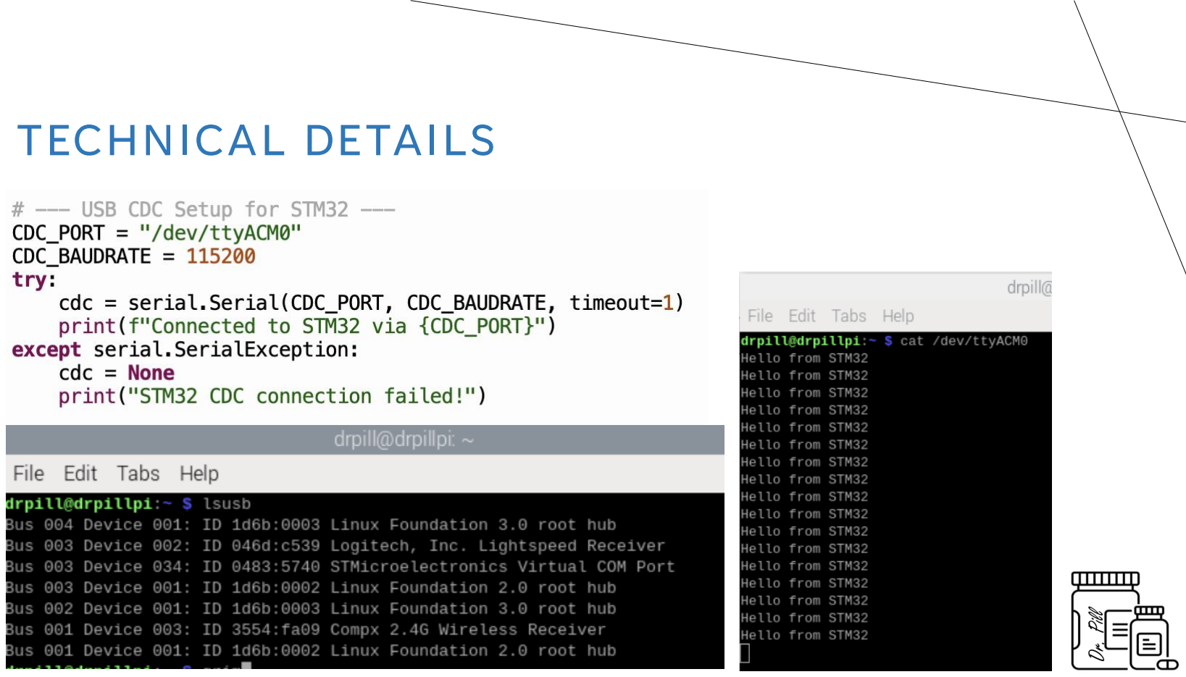
[picture p131: page 13]

13 Dr. Pill

## TECHNICAL DETAILS

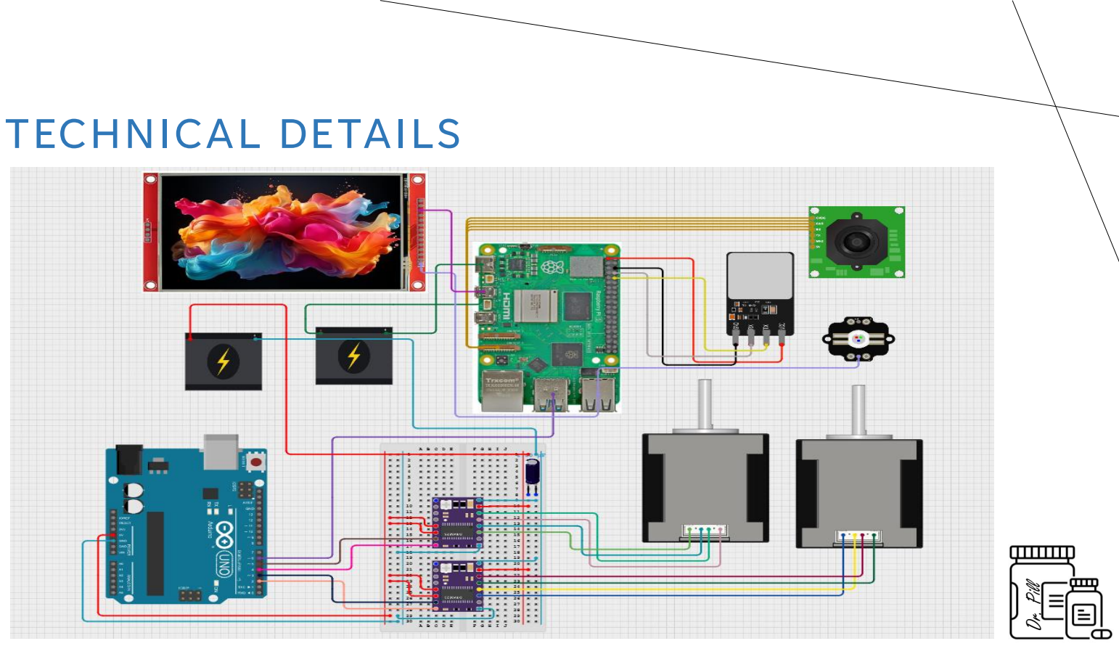
[picture p132: page 14]

14 Dr. Pill

## CHALLENGES

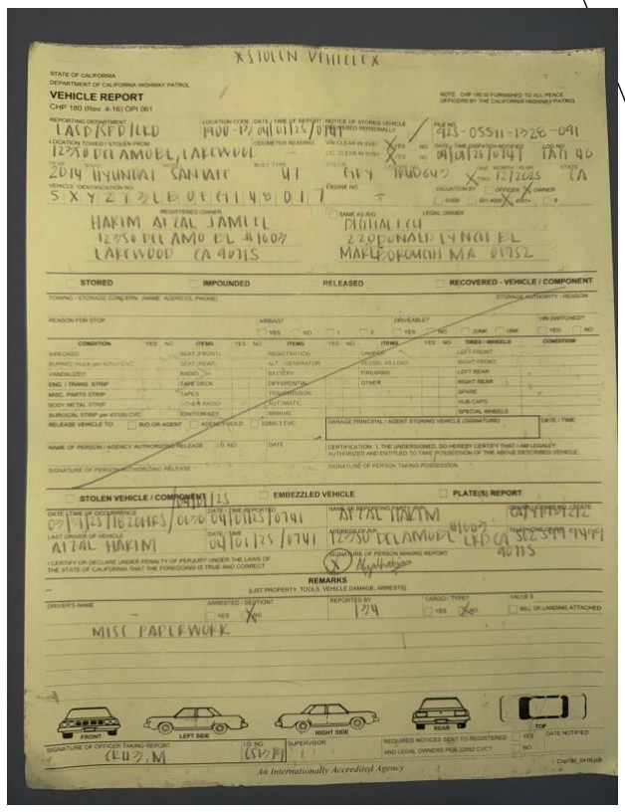
[picture p133: figure]

15 Dr. Pill

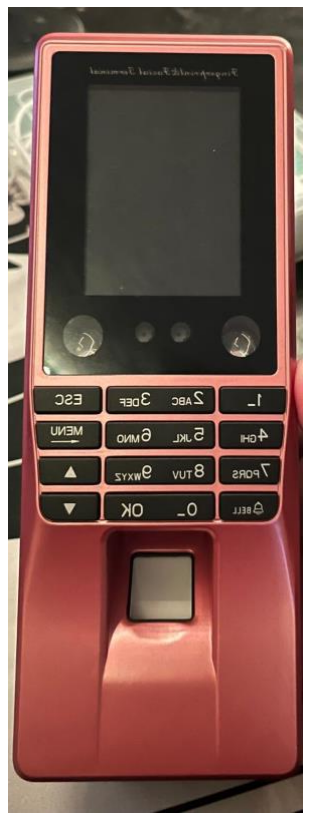
[picture p134: figure]

- Car got stolen – This unexpected event caused us delays as our fingerprint and facial recognition device was in the car that got stolen.
- New fingerprint and facial recognition devices – We switched to a new biometric device which required us to do more research and understand how to code and integrate it properly.
- Challenging to code – Writing the software to integrate all hardware components, especially the new security features was complex and time consuming.
- Pixy2 object recognition issue – The Pixy2 sensor detects pills based on color, so all white pills are being recognized as the same which made it hard for us to differentiate between 2 white colored pills. Lighting inconsistency obscured the camera's ability to recognize pills.
- Board-to-board communication difficulties – After setting up the fingerprint and facial recognition devices separately, making them work together across different boards caused integration issues.

## OVERCOMING CHALLENGES

16 Dr. Pill

- We ended up using camera module 2 and adafruit fingerprint scanner thats connected by strip cable, and fingerprint scanner by pins and uart, since the previous device is gone
- Trial and error with code and testing a number of commands in command prompt to identify the correct port for CDC setup for board to board communication
- The use of different colored pills to avoid the issue of inaccuracy in identifying pills. The Pixy2 camera has a built in light that we used for the main source of lighting

17

## FINAL DEMO

Dr. Pill

The complete device 'Dr. Pill' The Automatic Pill Dispenser

- Log Tracking – The system keeps a record of user interactions, pill dispensing events and authentication activity.
- Fully Completed GUI – A user friendly and responsive interface is ready making it easy for all users to navigate the system.
- Pill Dispensing with Object Recognition – Pills are dispensed automatically with the Pixy2 sensor confirming both the number and type of pills dispensed.

All components (GUI, fingerprint, face recognition, motors, pill sensor) working together seamlessly without manual intervention.


# THANK YOU

Dr. Pill
