JonTeaCz/CECS490-DR.PILL/Progress/Presentations/CECS 490B - Final Presentation.pdf

# DR. PILL

Automatic Pill Dispenser

## TEAM AND RESPONSIBILITIES

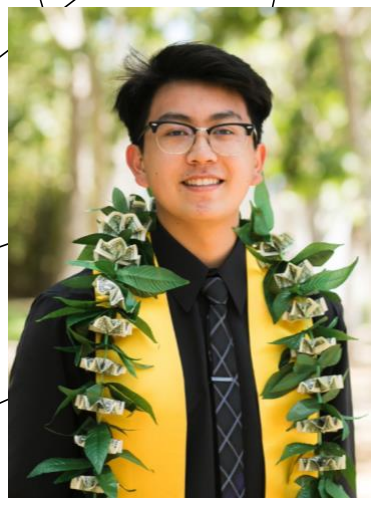
[picture p135: figure]

•Circuit
•Power Supply and
Regulation
•Fingerprint and
Facial Recognition

Jonathan
Cerniaz

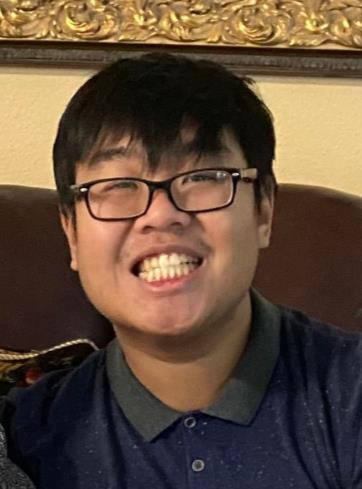
[picture p136: figure]

Jehmel
Espiritu


Jeremy
Espiritu

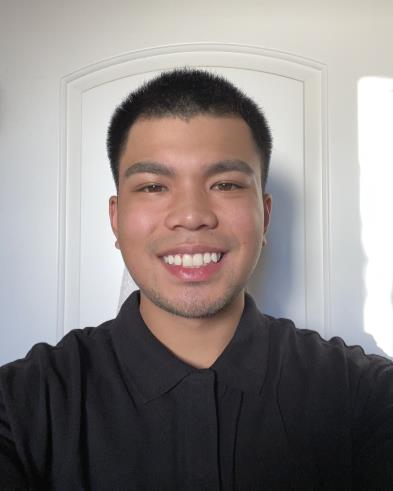
[picture p137: figure]

Joseph
Guzman

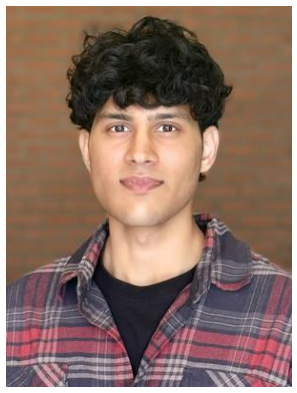
[picture p138: figure]

Afzal
Hakim


Lee Roger
Ordinario
- Software
Development
of Interface
- Fingerprint and
Facial Recognition
- Log tracking and
Security
- Pill Storage
System and
Organization
- Soldering
- Software
Development
of Interface
- Enclosure &
Framework
- 3D Design and Build
- Motor Testing &
Calibration


## Executive Summary

Dr. Pill

Dr. Pill is an automatic pill dispenser that simplifies medication management. Our device aims to facilitate the process by freeing up more time for doctors and allowing patients to take their medication accurately by eliminating the common issue of medication errors and missed dosages. Designated for pharmacies, nursing homes, personal households.

## OUR 3 DEMOS

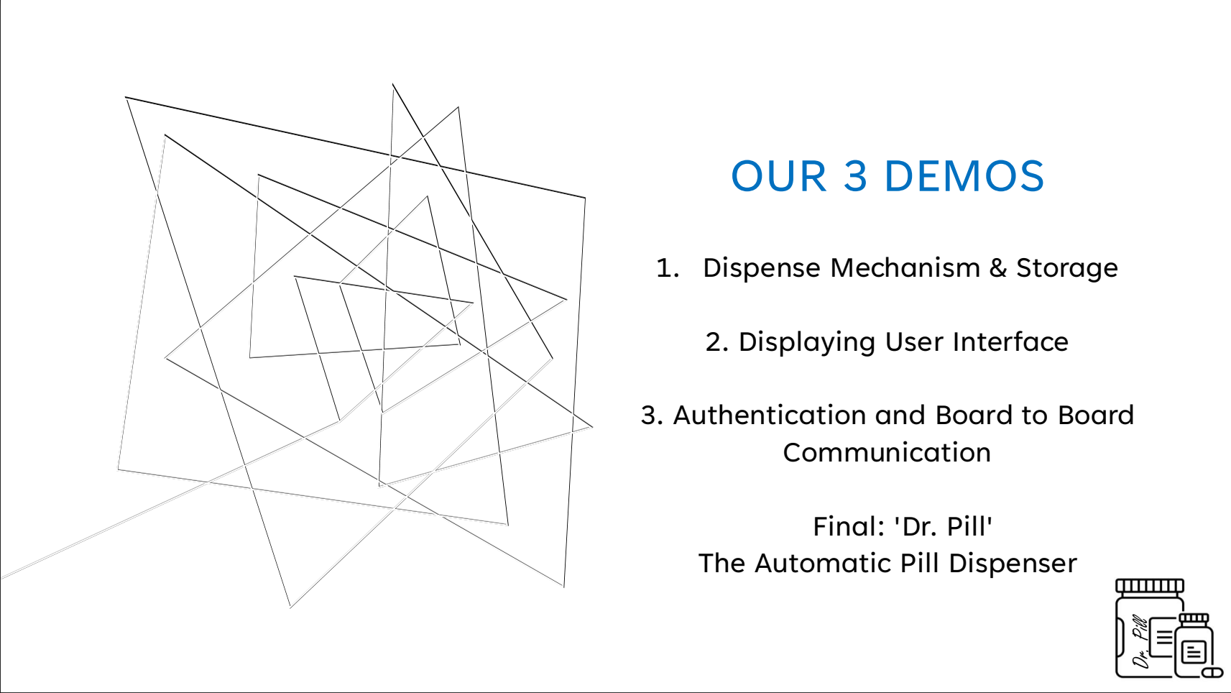
[picture p139: page 4]

Dr. Pill

1. Dispense Mechanism & Storage
2. Displaying User Interface
3. Authentication and Board to Board Communication

Final: 'Dr. Pill'
The Automatic Pill Dispenser

5

## FINAL DEMONSTRATION

'Dr. Pill' The Automatic Pill Dispenser

Requirements: Accumulation of all demos + Real-Time Logging, Add/Delete User, Conveyor Belt

Constraints: Log accuracy, facial and fingerprint recognition accuracy

Success: Logs show real-time activity, conveyor belt brings pills to the front, adding/deleting user

Dr. Pill


# DEMO TIME

## TECHNICAL DETAILS

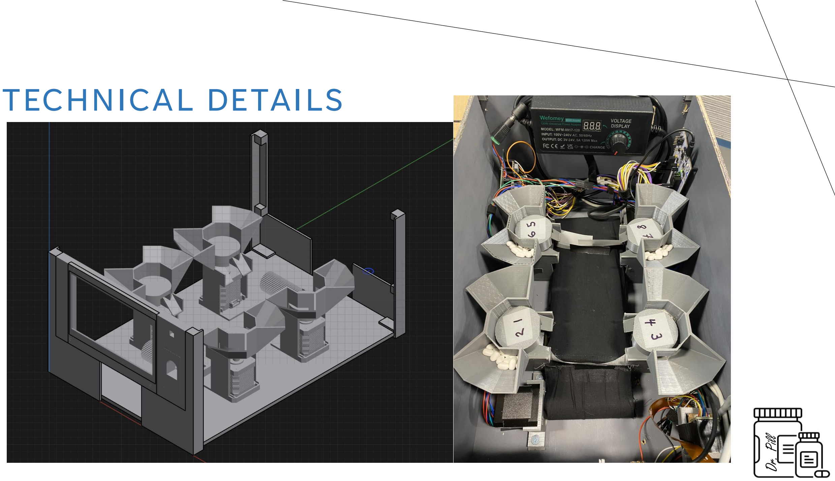
[picture p140: page 7]

7 Dr. Pill

## TECHNICAL DETAILS

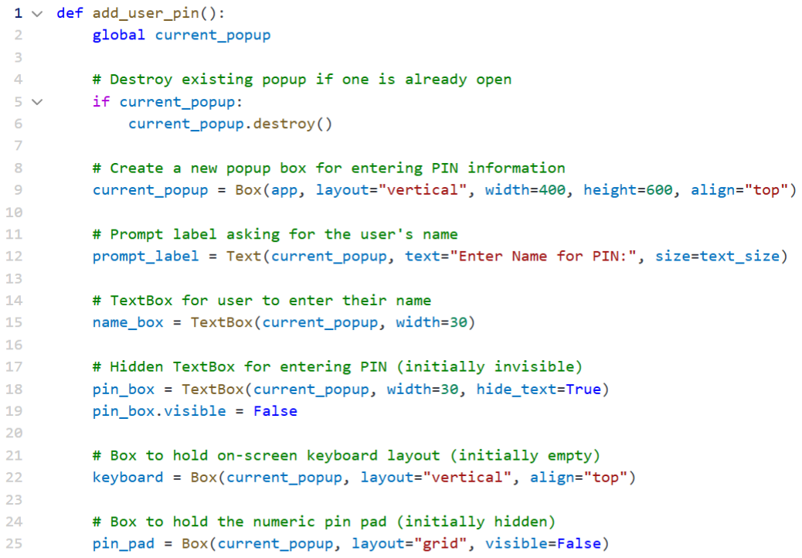
[picture p141: figure]

8 Dr. Pill

## TECHNICAL DETAILS

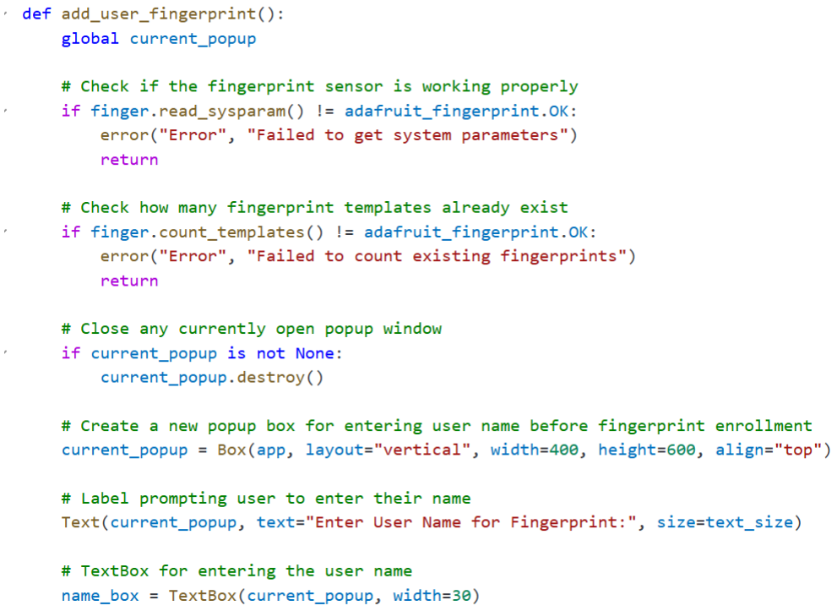
[picture p142: figure]

9 Dr. Pill

## TECHNICAL DETAILS

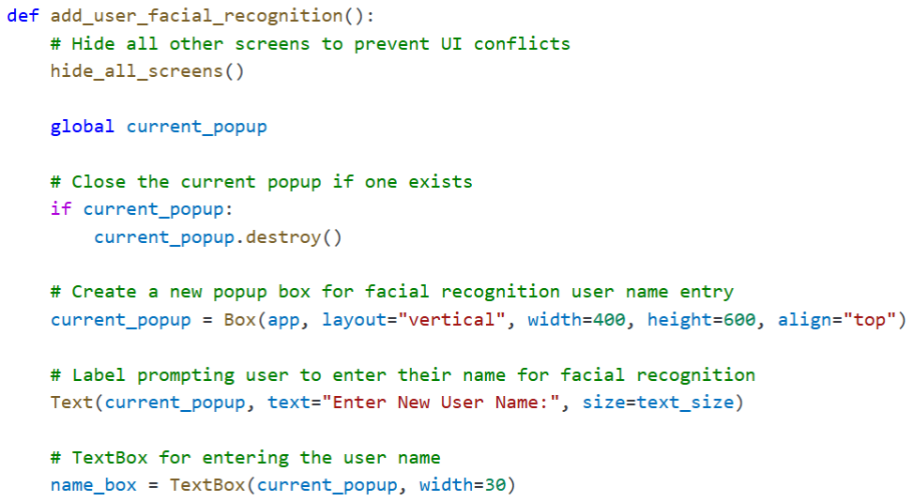
[picture p143: figure]

10 Dr. Pill

## TECHNICAL DETAILS

11 Dr. Pill

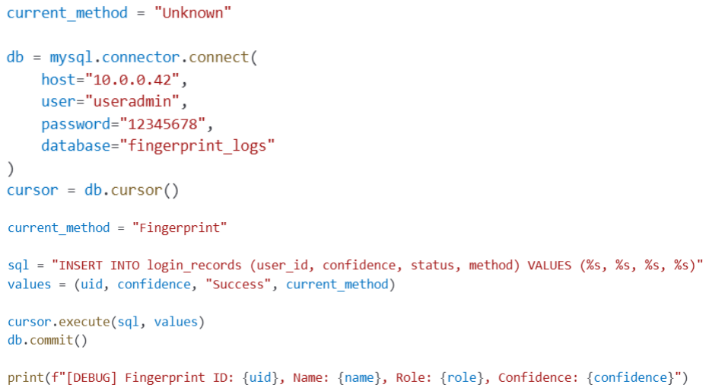
[picture p144: figure]

## TECHNICAL DETAILS

12 Dr. Pill

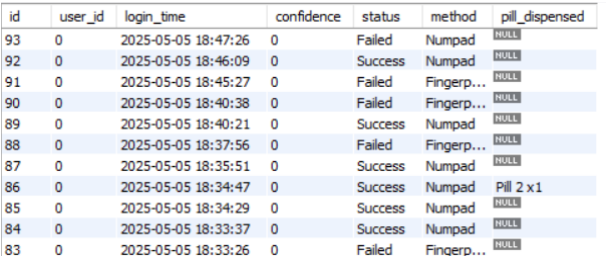
[picture p145: figure]

## TECHNICAL DETAILS


13 Dr. Pill

## CHALLENGES AND HOW WE SOLVED IT

14 Dr. Pill

- 3D printing issues (clogging, broken nozzel, poor print quality, etc.)
- Wi-fi connectivity (Mango Wi-fi router)
- Dispensing (Object recognition, jamming, pill size, and unpredictability)
- GUI (Crashing, quality of interface, and multiple menus)

15

## REFLECTION

Dr. Pill

- We all learned a lot from this class like learning how 3D print, creating logs with MySQL, Fingerprint and Facial Recognition, creating a custom GUI from scratch.
- We also learned the fundamentals of working as a team (team communication, time management, planning, etc.)
- Since we were only missing the object recognition that leaves us with 95% of the project being complete. If we were to continue this project there it a lot we could improve on in the future (Cleaner GUI, object recognition, better enclosure, etc.)


# THANK YOU

Dr. Pill
