JonTeaCz/CECS490-DR.PILL/Documentation/STM32_PINOUTS.pdf

# Zio an

d

A

r

d

# uin

o

c

o

m

p

a

# tible

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
y), (https://os.mbed.com/search/?q=ST%20Discovery) S

T

N

u

cle

o (https://os.mbed.com/search/?q=ST%20Nucleo) (/s

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
o) (https://os.mbed.com/search/?q=ST%20Nucleo) Last updated: 2

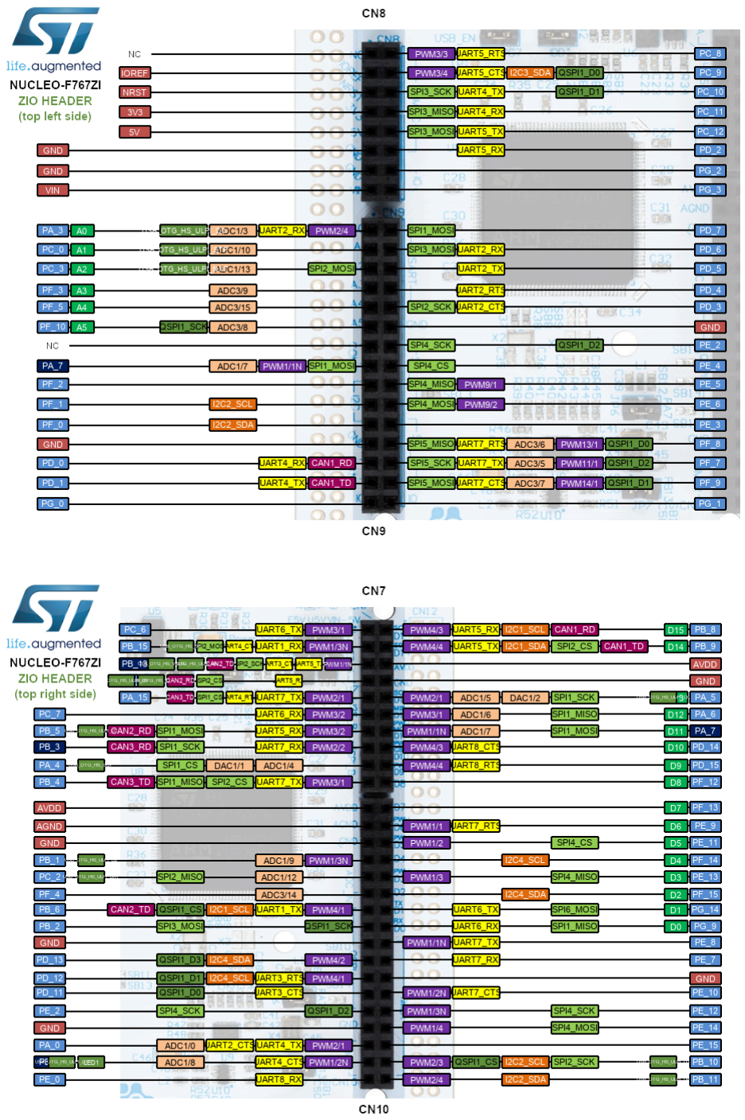
[picture p156: figure]

7

M

a

r

2

0

1

9 (2

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
